OmerFaruk-Celik/ATILAY/atilay_kodlar/image.png

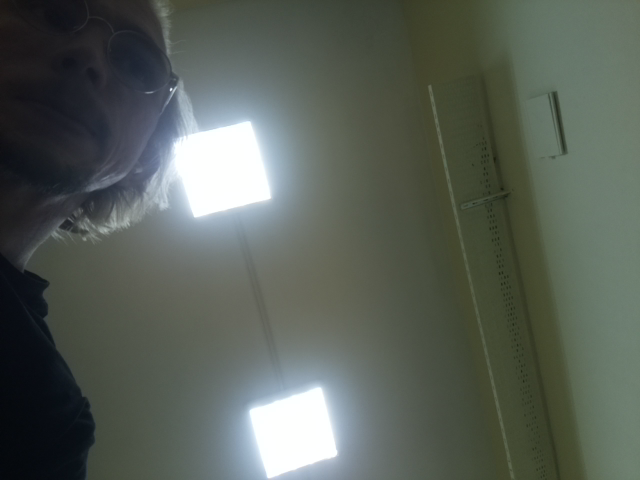
atilay_kodlar/image.png
