OmerFaruk-Celik/ATILAY/ProjeResimleri/IMG-20240529-WA0002.jpg

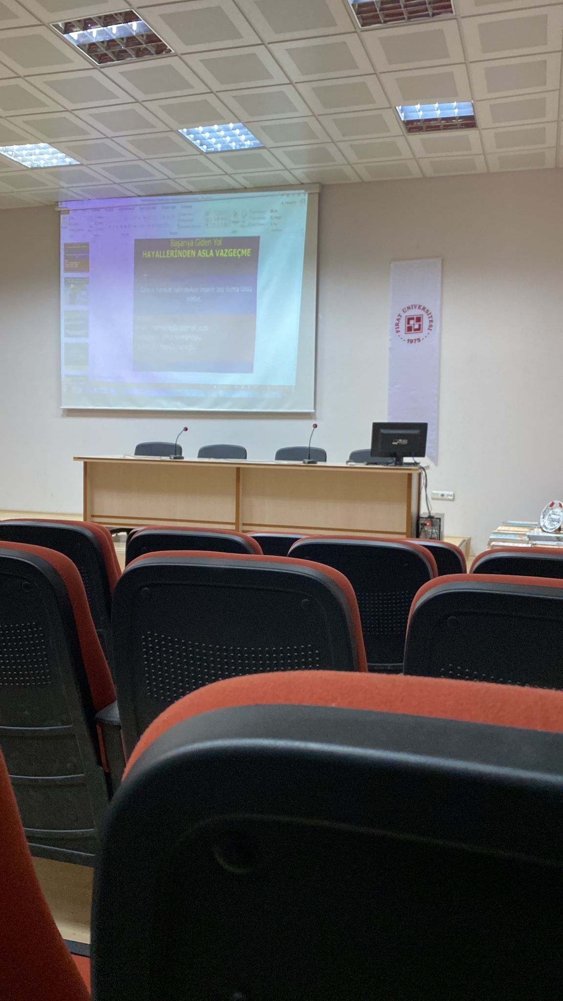
ProjeResimleri/IMG-20240529-WA0002.jpg
