OmerFaruk-Celik/ATILAY/ProjeResimleri/IMG-20240602-WA0001.jpg

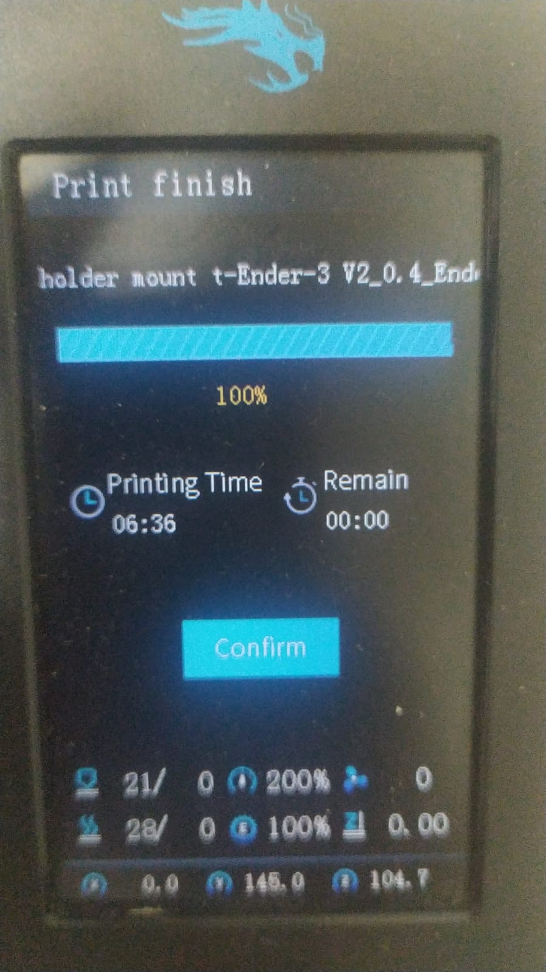
ProjeResimleri/IMG-20240602-WA0001.jpg
