OmerFaruk-Celik/ATILAY/ProjeResimleri/IMG-20240603-WA0001.jpg

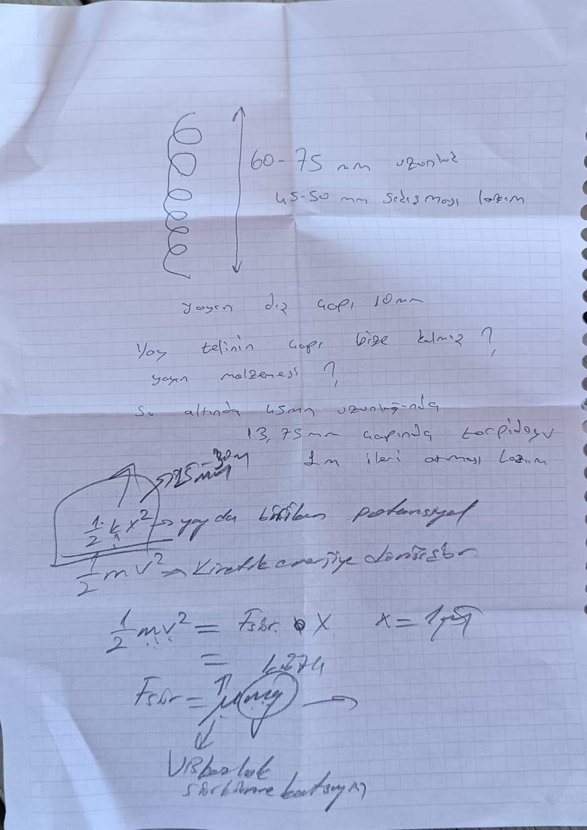
ProjeResimleri/IMG-20240603-WA0001.jpg
