OmerFaruk-Celik/ATILAY/ProjeResimleri/IMG-20240604-WA0000.jpg

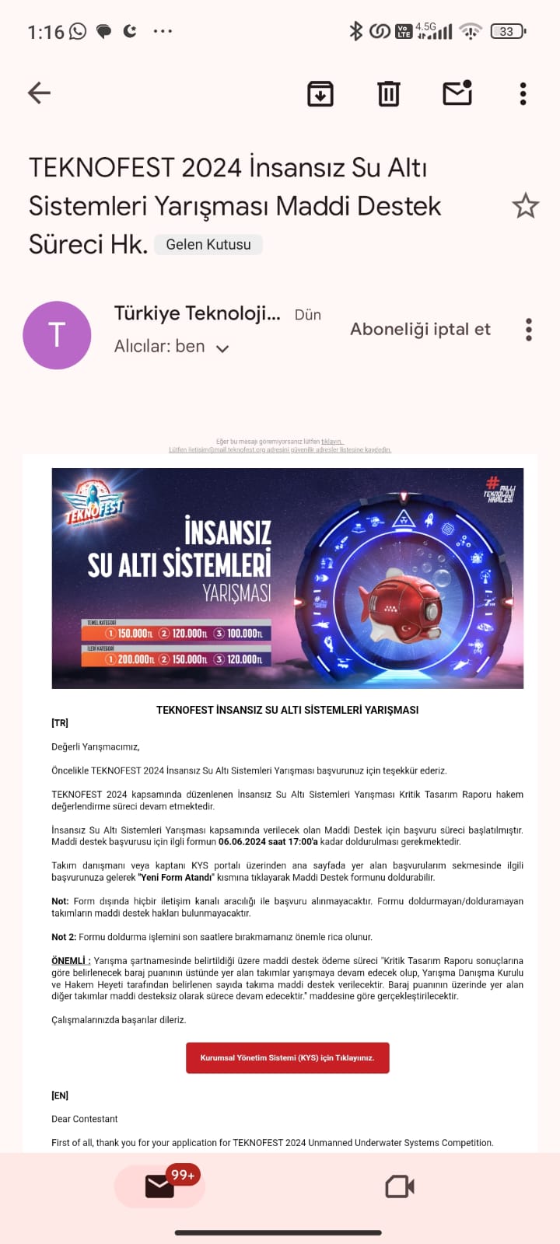
ProjeResimleri/IMG-20240604-WA0000.jpg
