OmerFaruk-Celik/ATILAY/ProjeResimleri/IMG-20240604-WA0001.jpg

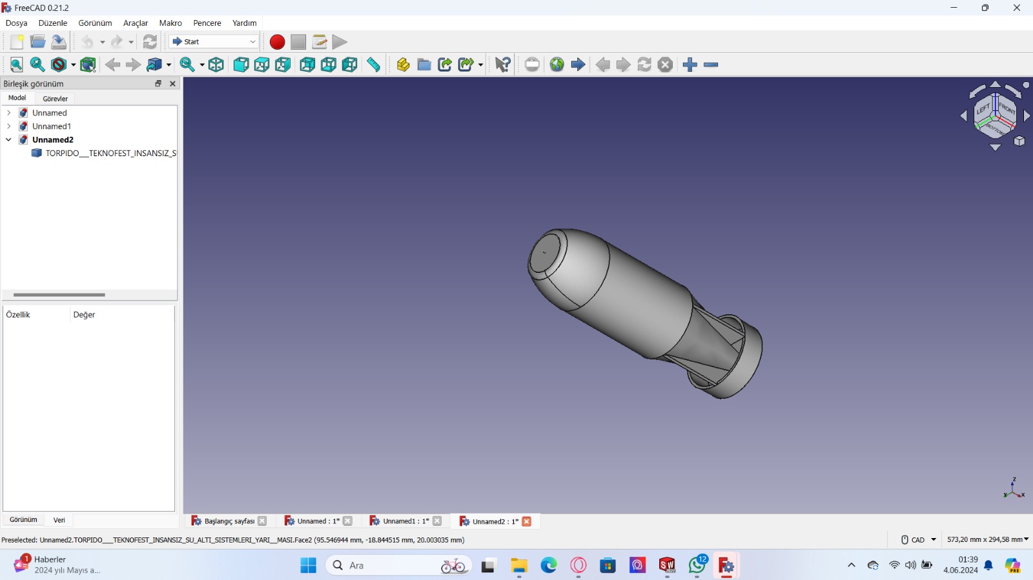
ProjeResimleri/IMG-20240604-WA0001.jpg
