OmerFaruk-Celik/ATILAY/ProjeResimleri/IMG-20240604-WA0003.jpg

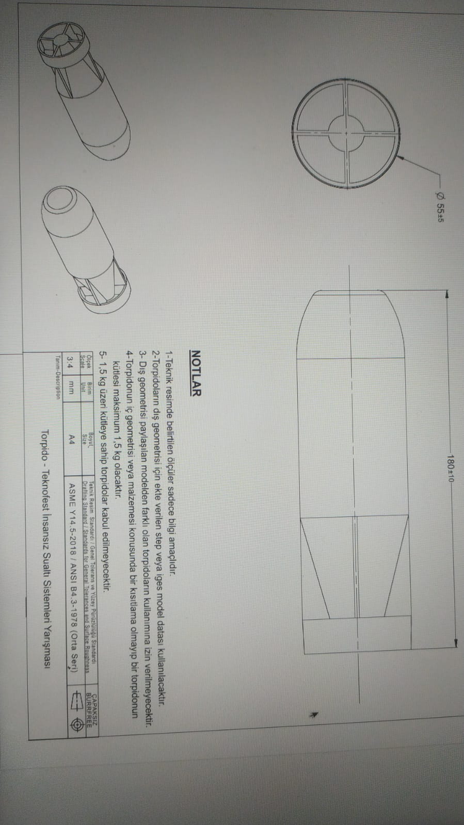
ProjeResimleri/IMG-20240604-WA0003.jpg
