OmerFaruk-Celik/ATILAY/ProjeResimleri/IMG-20240604-WA0005.jpg

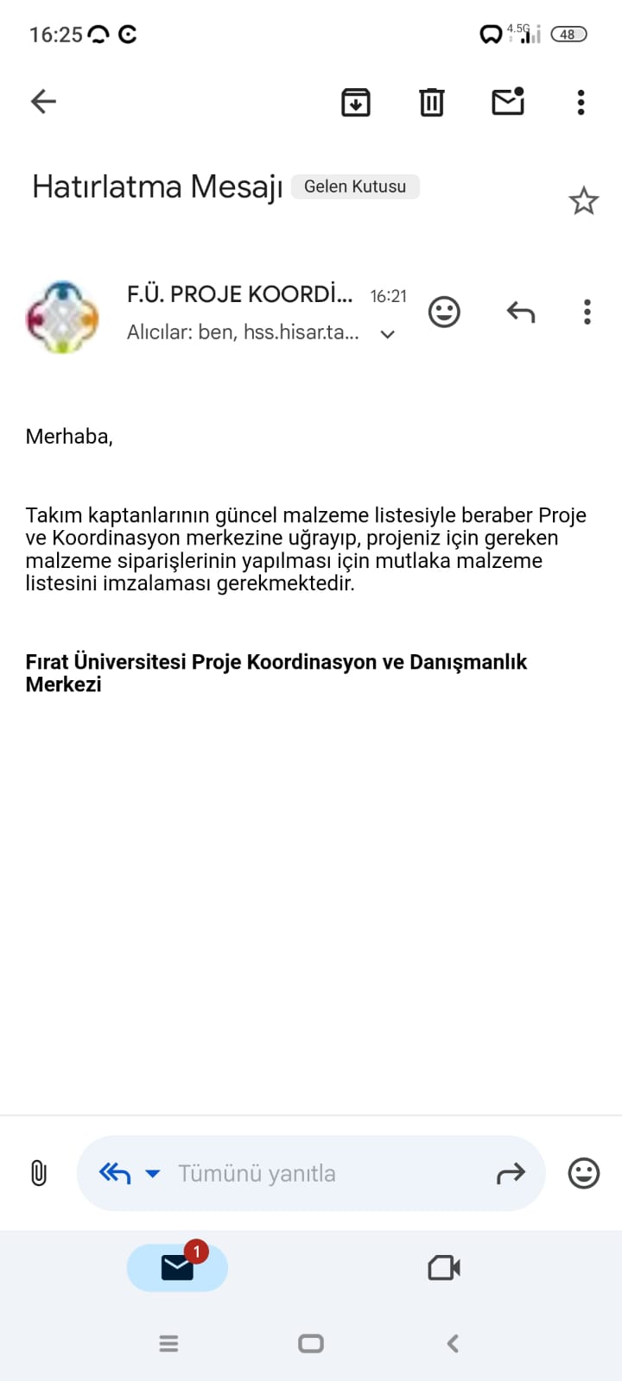
ProjeResimleri/IMG-20240604-WA0005.jpg
