OmerFaruk-Celik/ATILAY/ProjeResimleri/IMG-20240604-WA0007.jpg

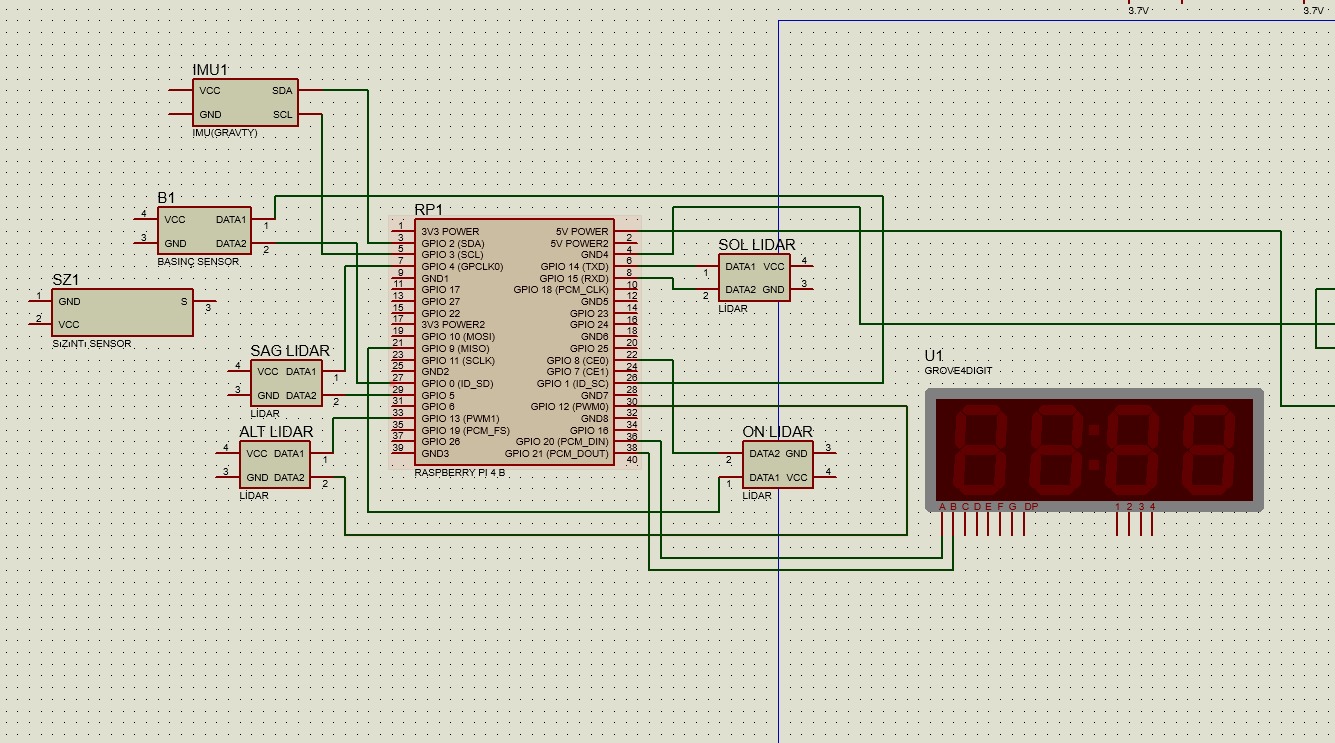
ProjeResimleri/IMG-20240604-WA0007.jpg
