OmerFaruk-Celik/ATILAY/ProjeResimleri/IMG-20240604-WA0008.jpg

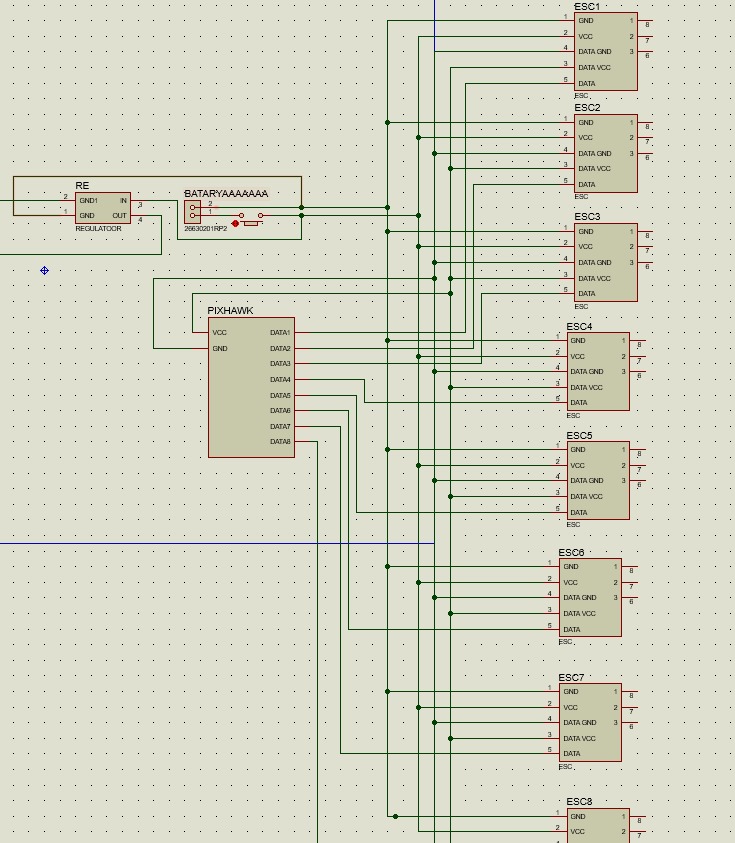
ProjeResimleri/IMG-20240604-WA0008.jpg
