OmerFaruk-Celik/ATILAY/ProjeResimleri/IMG-20240604-WA0009.jpg

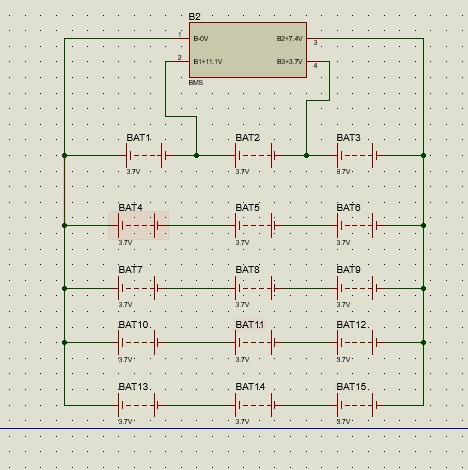
ProjeResimleri/IMG-20240604-WA0009.jpg
