OmerFaruk-Celik/ATILAY/ProjeResimleri/IMG-20240604-WA0010.jpg

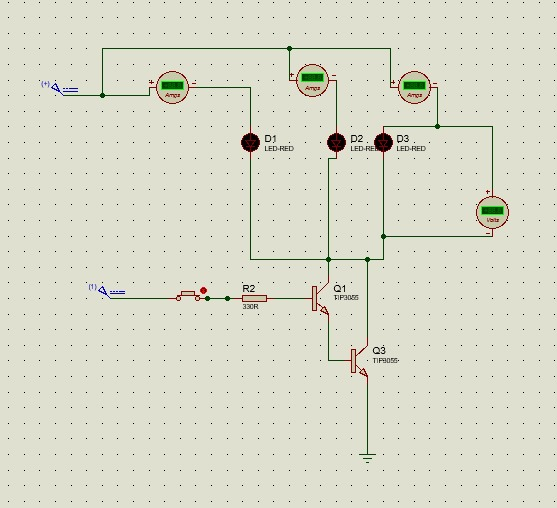
ProjeResimleri/IMG-20240604-WA0010.jpg
