OmerFaruk-Celik/ATILAY/ProjeResimleri/IMG-20240604-WA0011.jpg

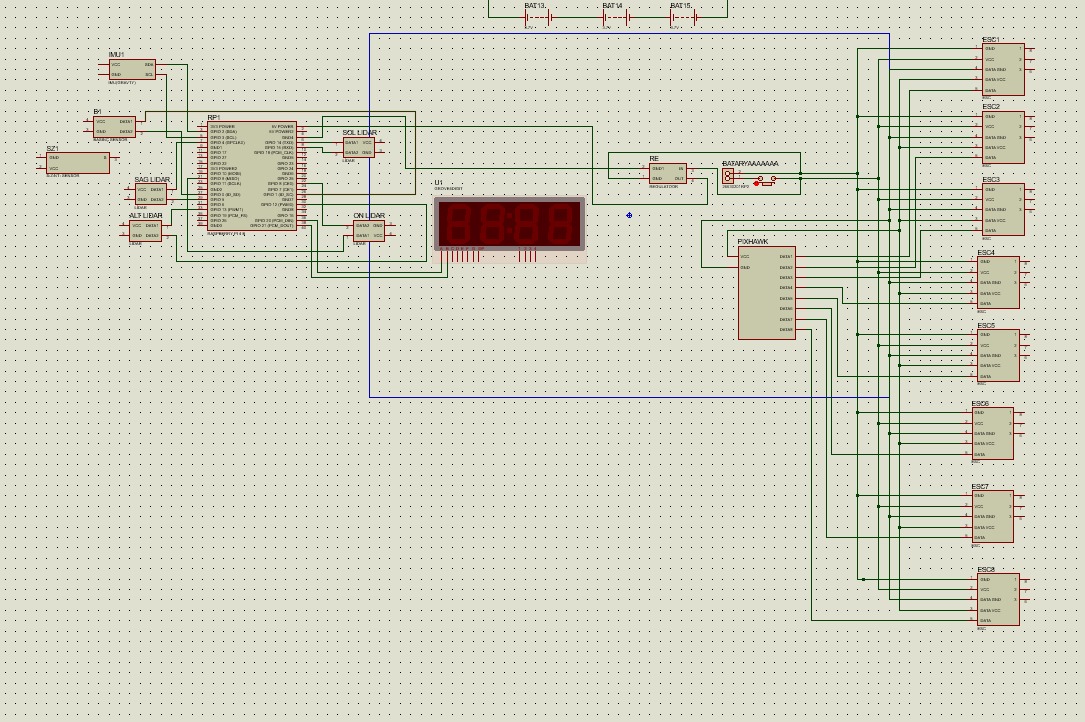
ProjeResimleri/IMG-20240604-WA0011.jpg
