OmerFaruk-Celik/ATILAY/ProjeResimleri/IMG-20240604-WA0039.jpg

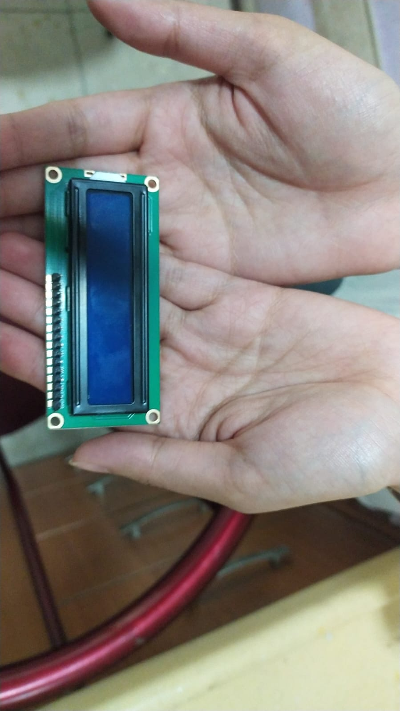
ProjeResimleri/IMG-20240604-WA0039.jpg
