OmerFaruk-Celik/ATILAY/ProjeResimleri/IMG-20240604-WA0040.jpg

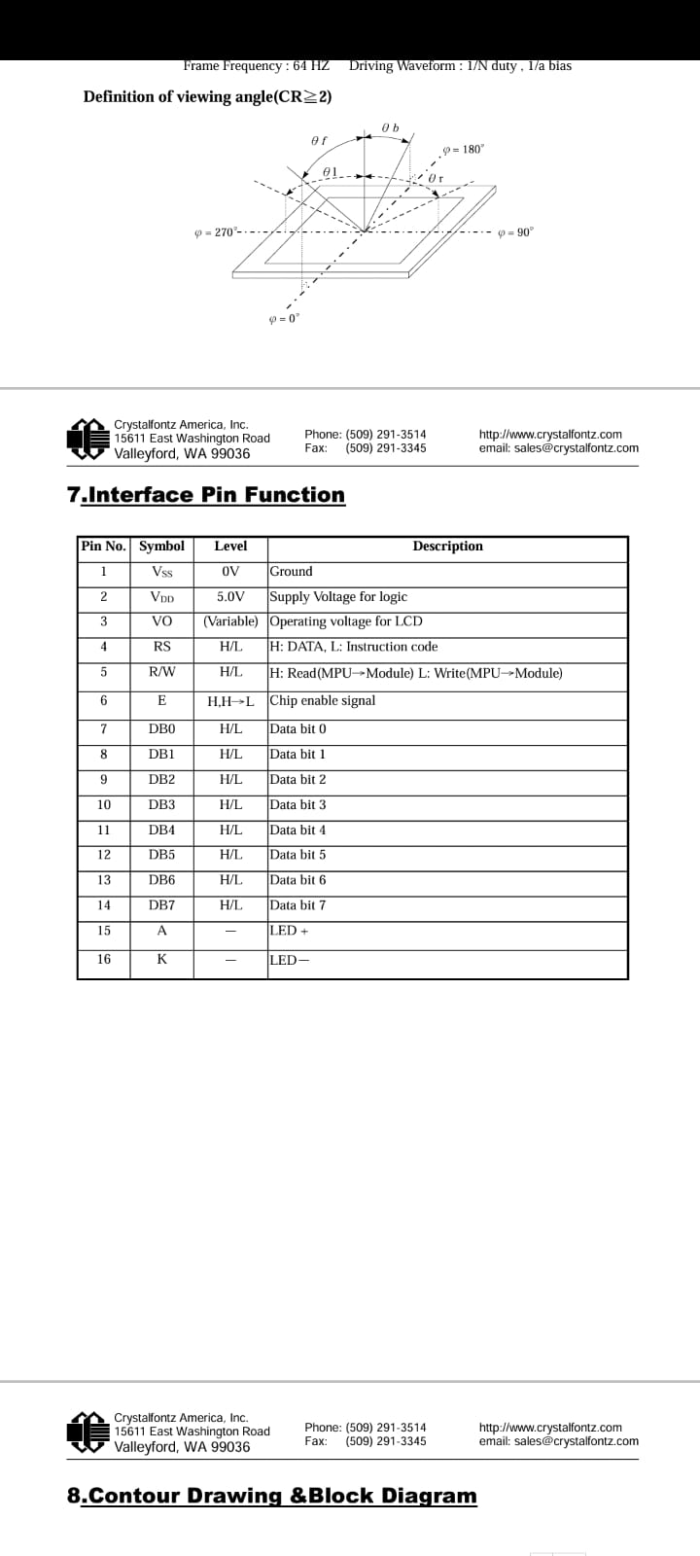
ProjeResimleri/IMG-20240604-WA0040.jpg
