OmerFaruk-Celik/ATILAY/ProjeResimleri/IMG-20240606-WA0000.jpg

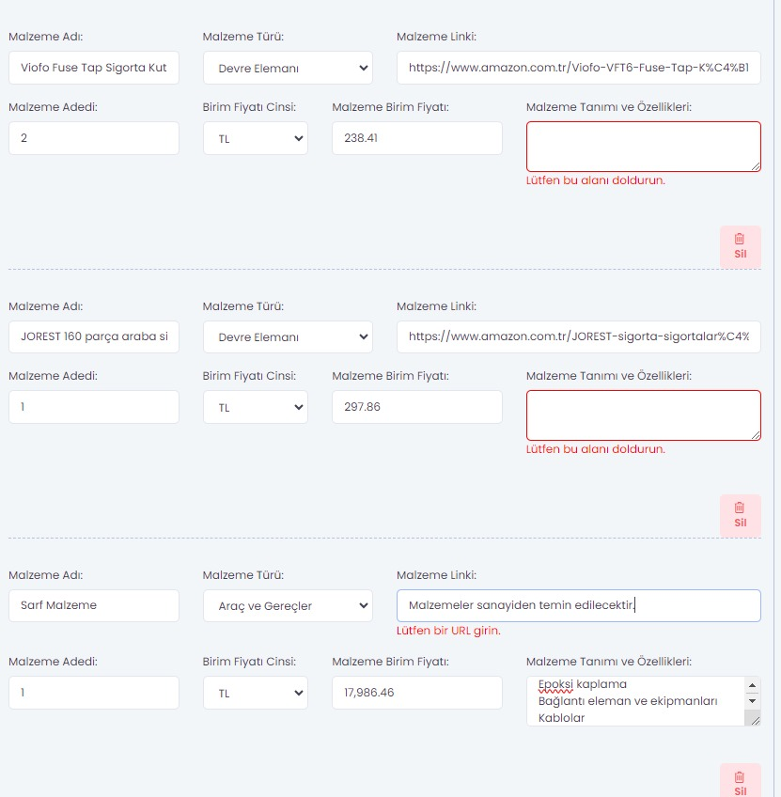
ProjeResimleri/IMG-20240606-WA0000.jpg
