OmerFaruk-Celik/ATILAY/ProjeResimleri/IMG-20240606-WA0001.jpg

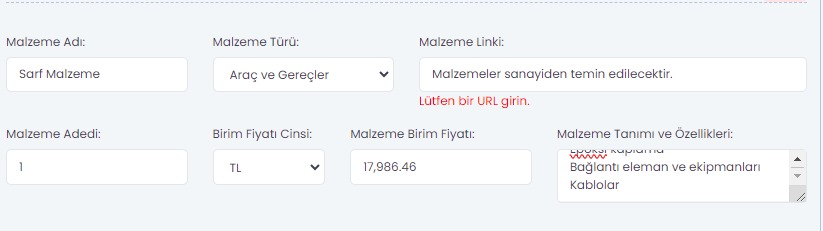
ProjeResimleri/IMG-20240606-WA0001.jpg
