OmerFaruk-Celik/ATILAY/ProjeResimleri/IMG-20240608-WA0016.jpg

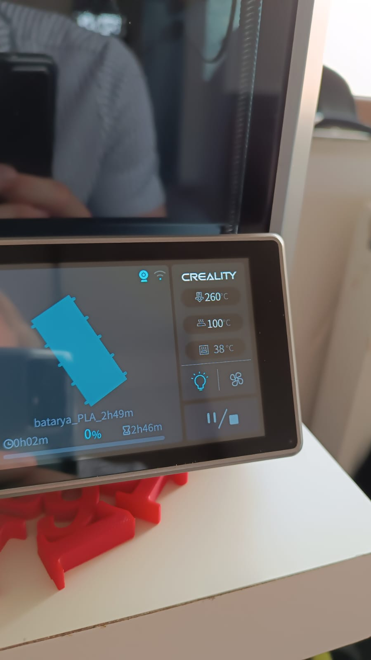
ProjeResimleri/IMG-20240608-WA0016.jpg
