OmerFaruk-Celik/ATILAY/ProjeResimleri/IMG-20240608-WA0018.jpg

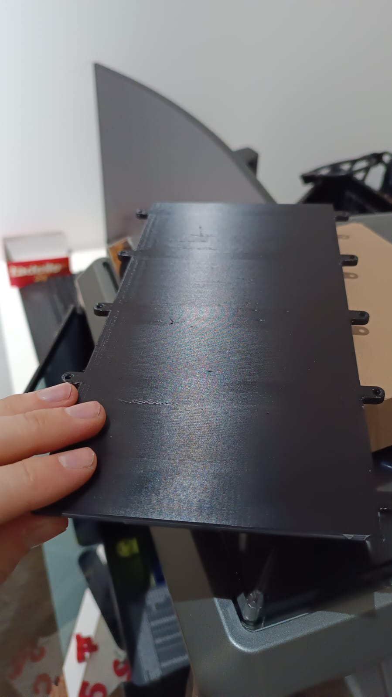
ProjeResimleri/IMG-20240608-WA0018.jpg
