OmerFaruk-Celik/ATILAY/ProjeResimleri/IMG-20240608-WA0019.jpg

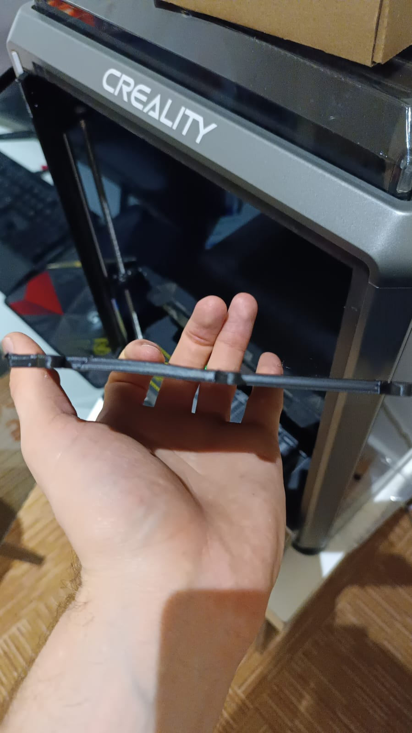
ProjeResimleri/IMG-20240608-WA0019.jpg
