OmerFaruk-Celik/ATILAY/ProjeResimleri/IMG-20240609-WA0012.jpg

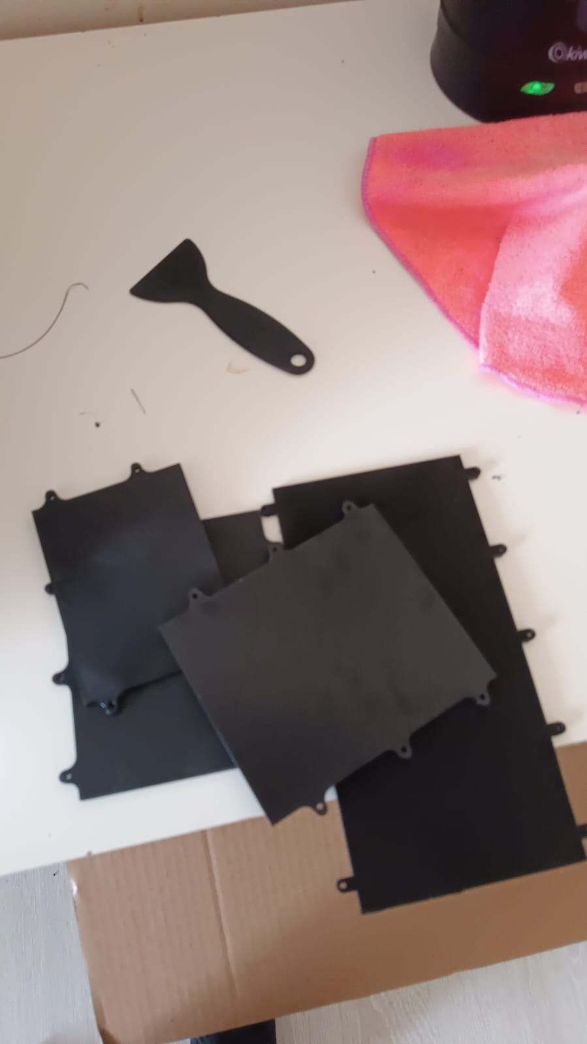
ProjeResimleri/IMG-20240609-WA0012.jpg
