OmerFaruk-Celik/ATILAY/ProjeResimleri/IMG-20240609-WA0013.jpg

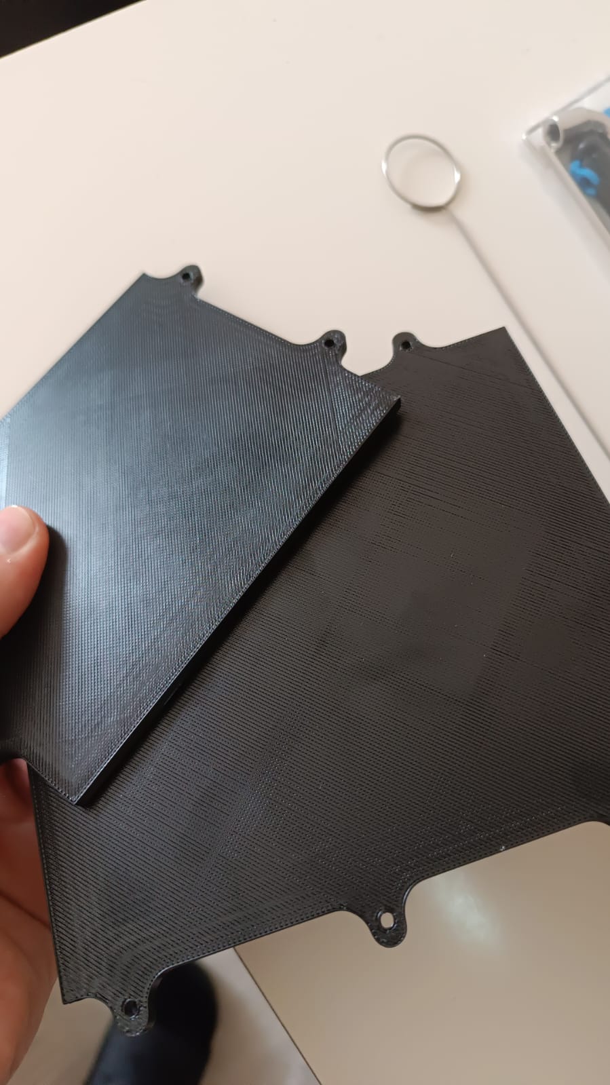
ProjeResimleri/IMG-20240609-WA0013.jpg
