OmerFaruk-Celik/ATILAY/ProjeResimleri/IMG-20240609-WA0015.jpg

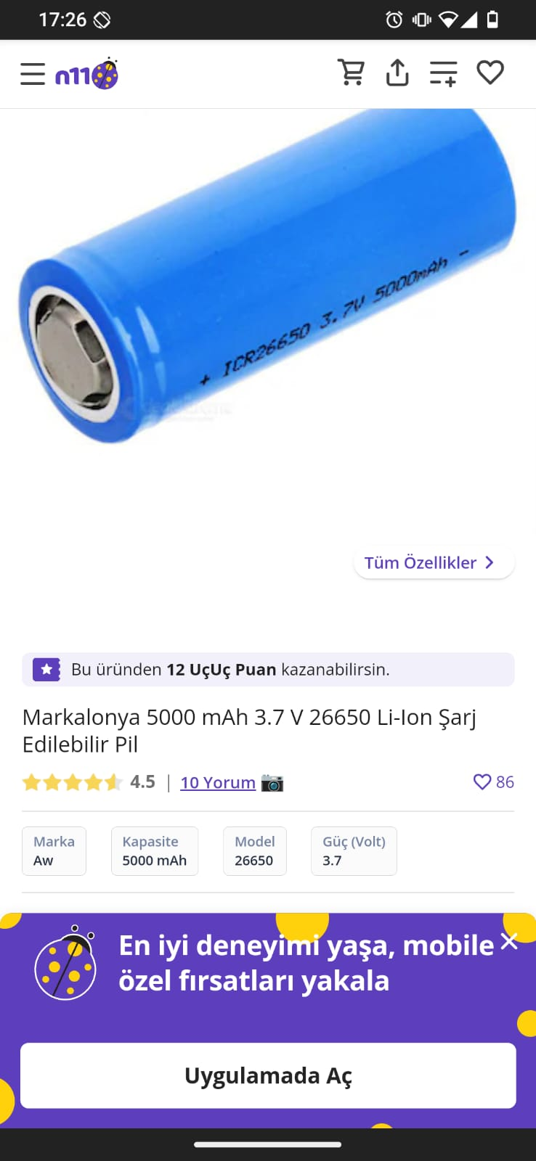
ProjeResimleri/IMG-20240609-WA0015.jpg
