OmerFaruk-Celik/ATILAY/ProjeResimleri/IMG-20240609-WA0017.jpg

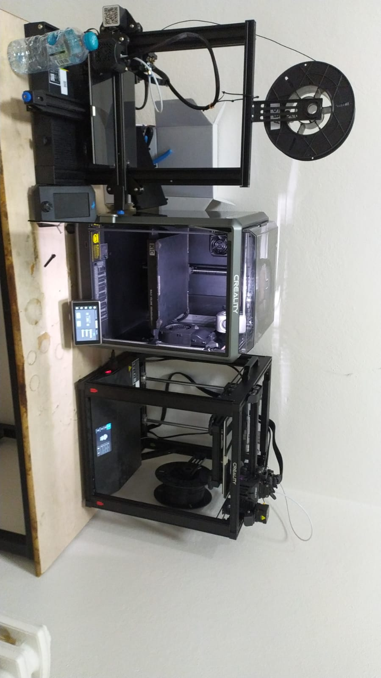
ProjeResimleri/IMG-20240609-WA0017.jpg
