OmerFaruk-Celik/ATILAY/ProjeResimleri/IMG-20240610-WA0000.jpg

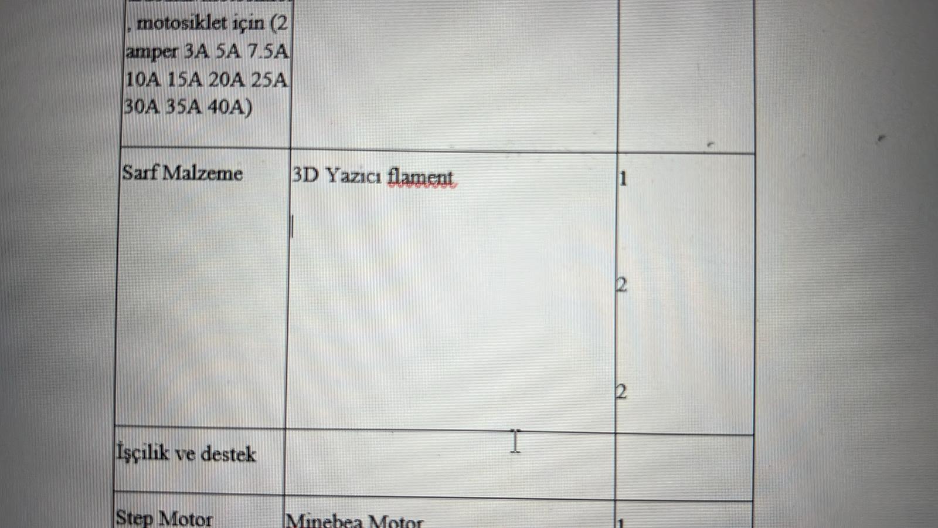
ProjeResimleri/IMG-20240610-WA0000.jpg
