OmerFaruk-Celik/ATILAY/ProjeResimleri/IMG-20240610-WA0002.jpg

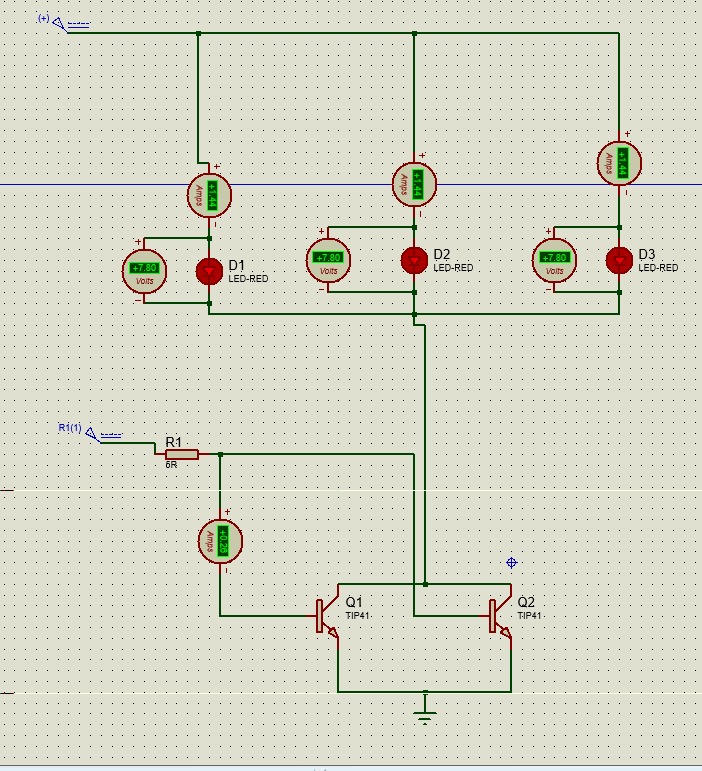
ProjeResimleri/IMG-20240610-WA0002.jpg
