OmerFaruk-Celik/ATILAY/ProjeResimleri/IMG-20240610-WA0004.jpg

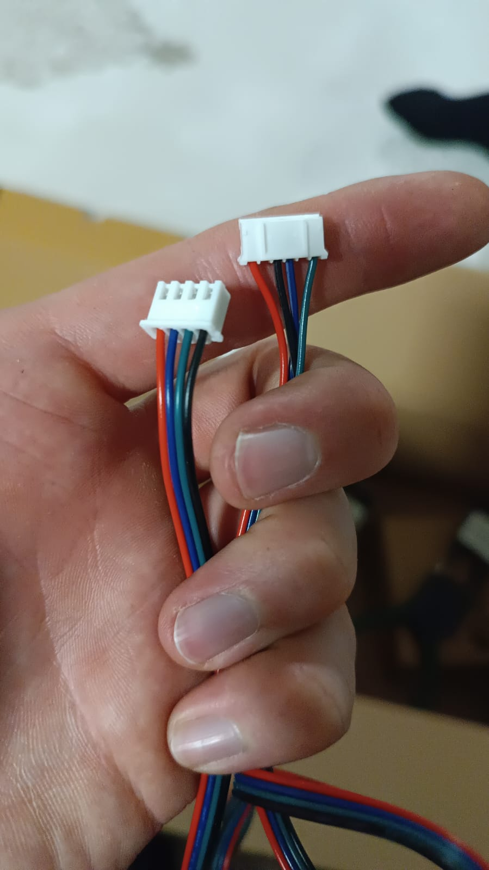
ProjeResimleri/IMG-20240610-WA0004.jpg
