OmerFaruk-Celik/ATILAY/ProjeResimleri/IMG-20240610-WA0005.jpg

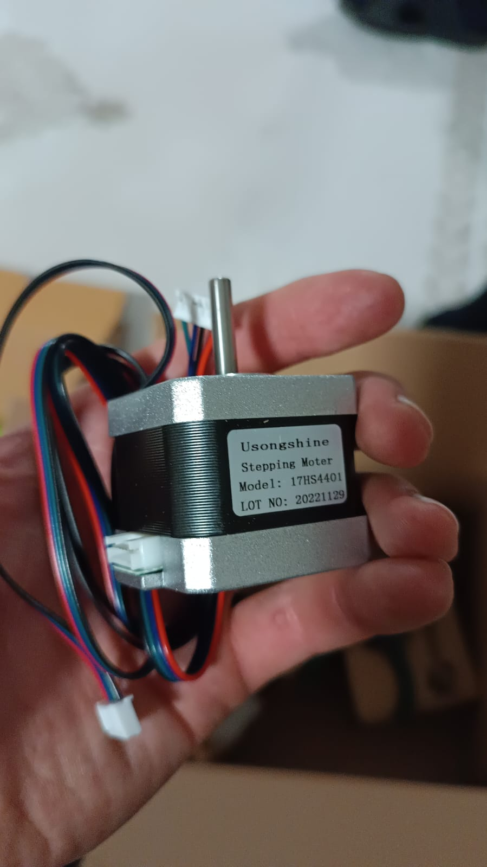
ProjeResimleri/IMG-20240610-WA0005.jpg
