OmerFaruk-Celik/ATILAY/ProjeResimleri/IMG-20240611-WA0004.jpg

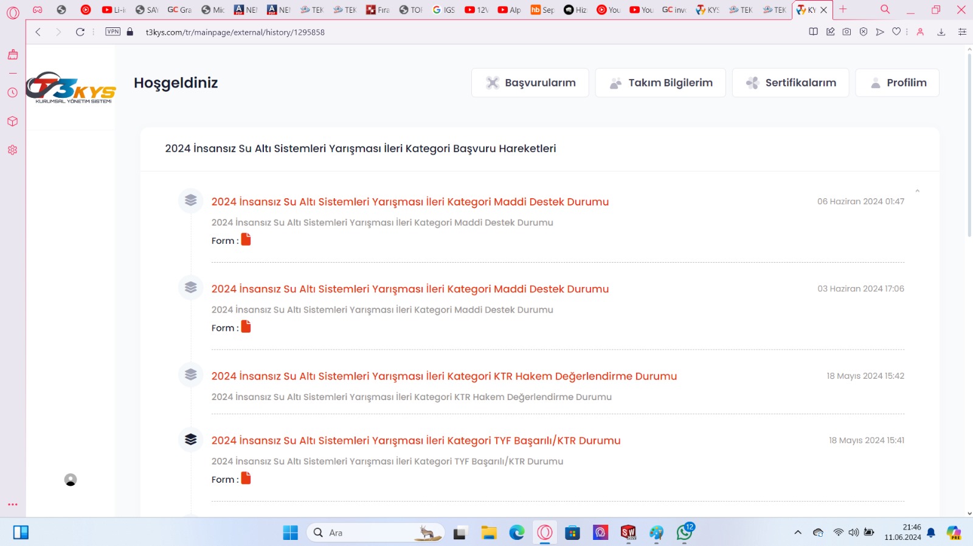
ProjeResimleri/IMG-20240611-WA0004.jpg
