OmerFaruk-Celik/ATILAY/ProjeResimleri/IMG-20240611-WA0006.jpg

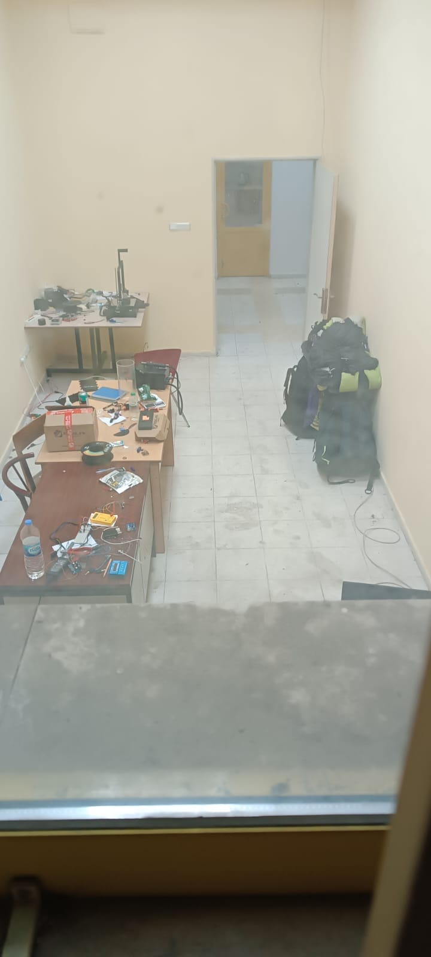
ProjeResimleri/IMG-20240611-WA0006.jpg
