OmerFaruk-Celik/ATILAY/ProjeResimleri/IMG-20240612-WA0005.jpg

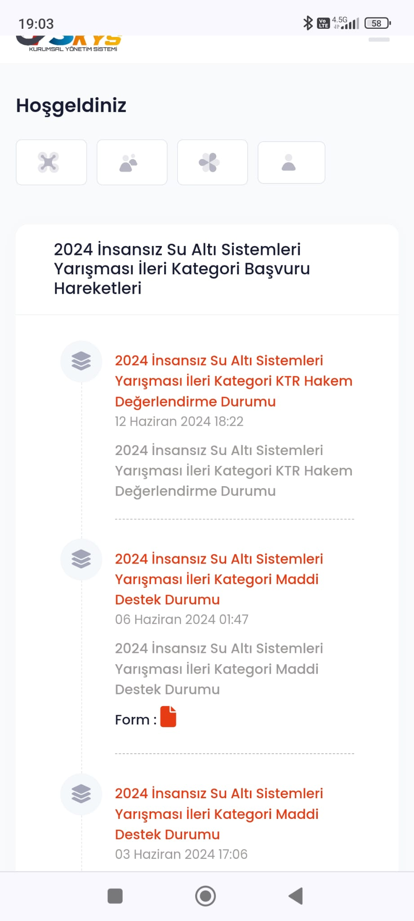
ProjeResimleri/IMG-20240612-WA0005.jpg
