OmerFaruk-Celik/ATILAY/ProjeResimleri/IMG-20240613-WA0009.jpg

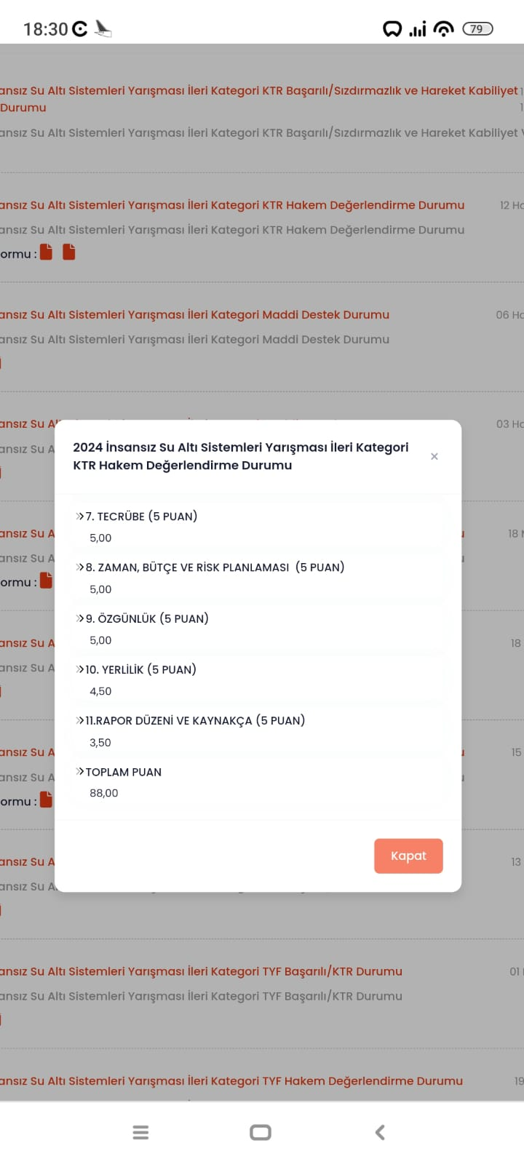
ProjeResimleri/IMG-20240613-WA0009.jpg
