OmerFaruk-Celik/ATILAY/ProjeResimleri/IMG-20240613-WA0010.jpg

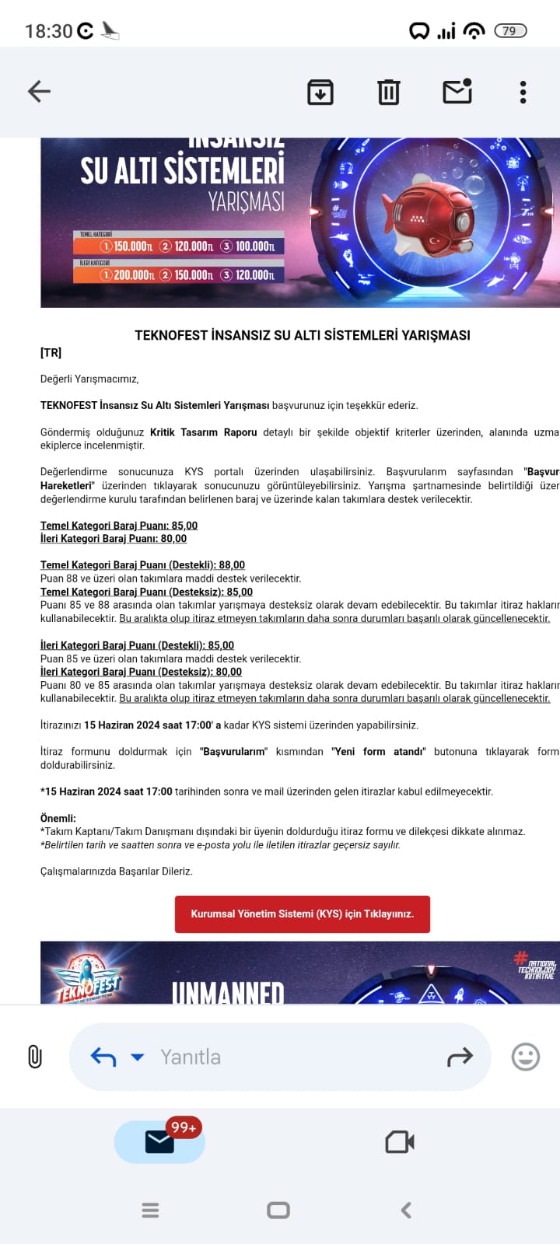
ProjeResimleri/IMG-20240613-WA0010.jpg
