OmerFaruk-Celik/ATILAY/ProjeResimleri/IMG-20240613-WA0028.jpg

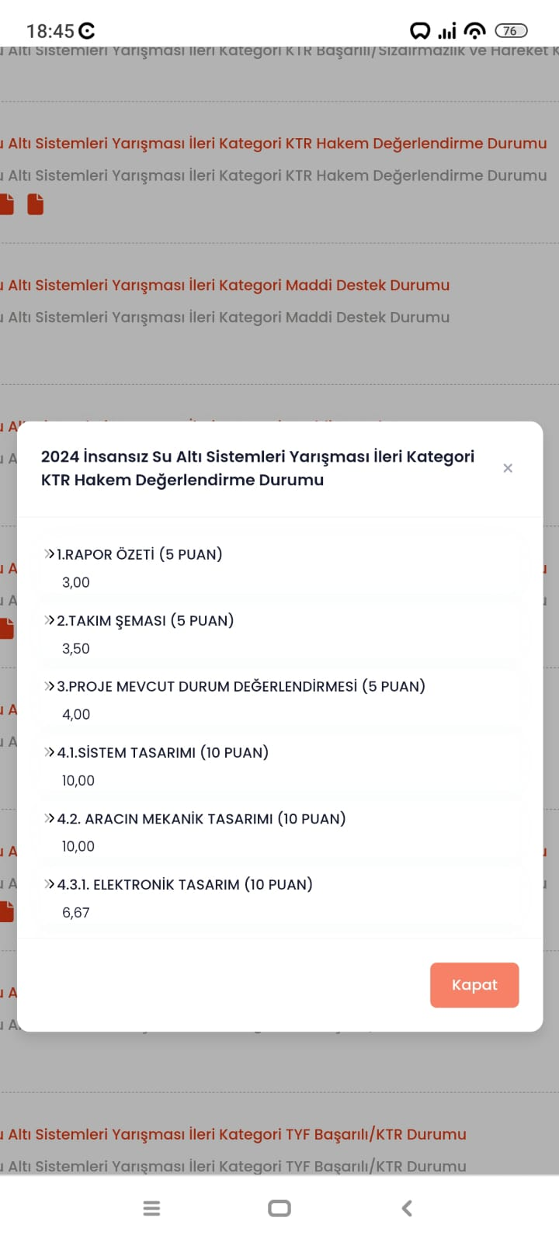
ProjeResimleri/IMG-20240613-WA0028.jpg
