OmerFaruk-Celik/ATILAY/ProjeResimleri/IMG-20240613-WA0029.jpg

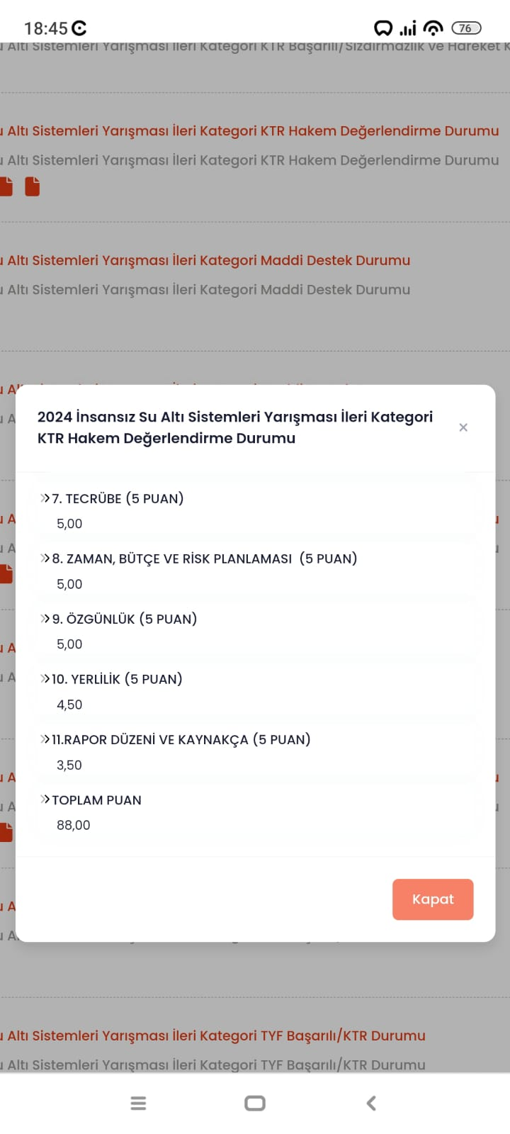
ProjeResimleri/IMG-20240613-WA0029.jpg
