OmerFaruk-Celik/ATILAY/ProjeResimleri/IMG-20240613-WA0030.jpg

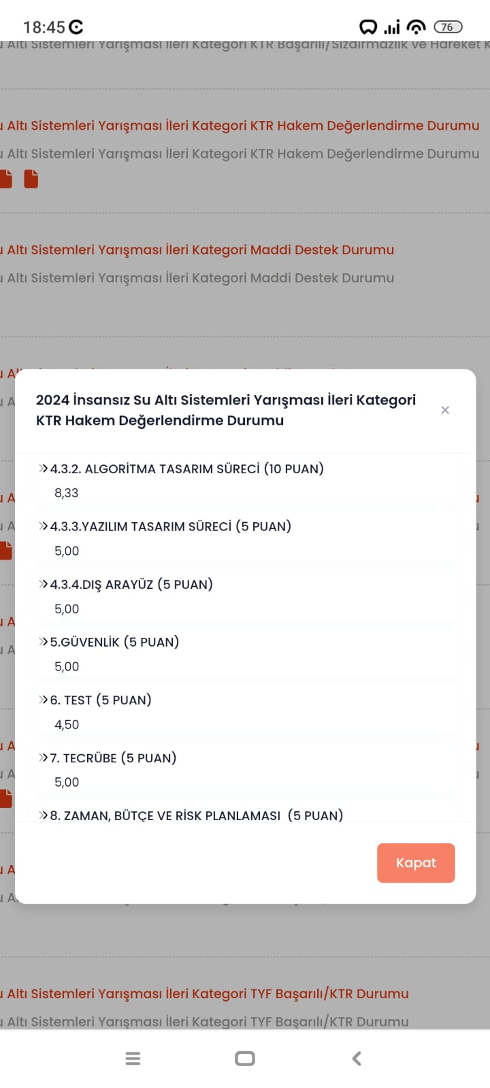
ProjeResimleri/IMG-20240613-WA0030.jpg
