OmerFaruk-Celik/ATILAY/ProjeResimleri/IMG-20240614-WA0005.jpg

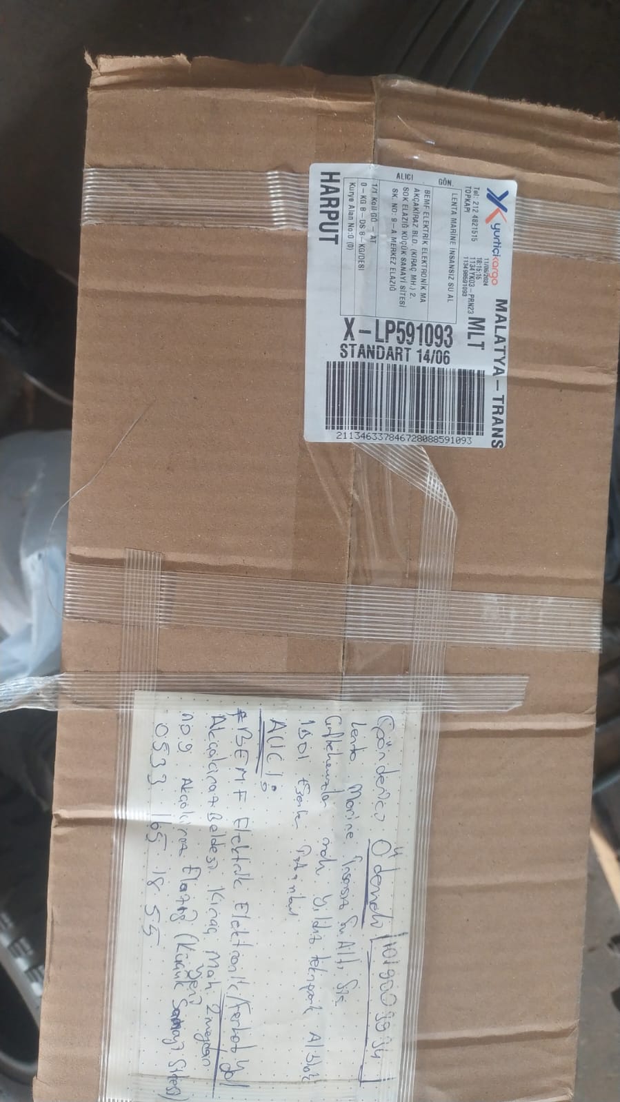
ProjeResimleri/IMG-20240614-WA0005.jpg
