OmerFaruk-Celik/ATILAY/ProjeResimleri/IMG-20240627-WA0004.jpg

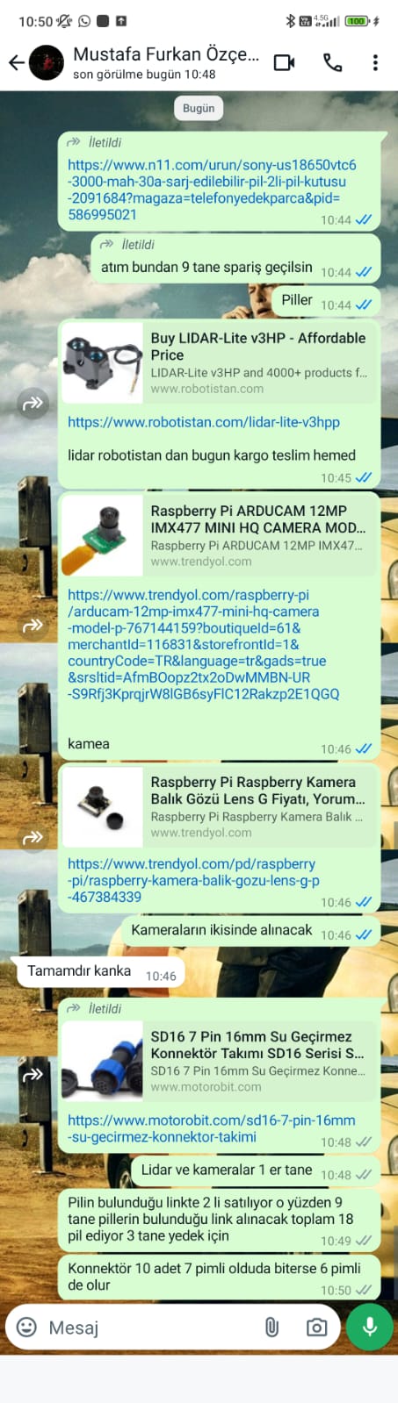
ProjeResimleri/IMG-20240627-WA0004.jpg
