OmerFaruk-Celik/ATILAY/ProjeResimleri/IMG-20240627-WA0005.jpg

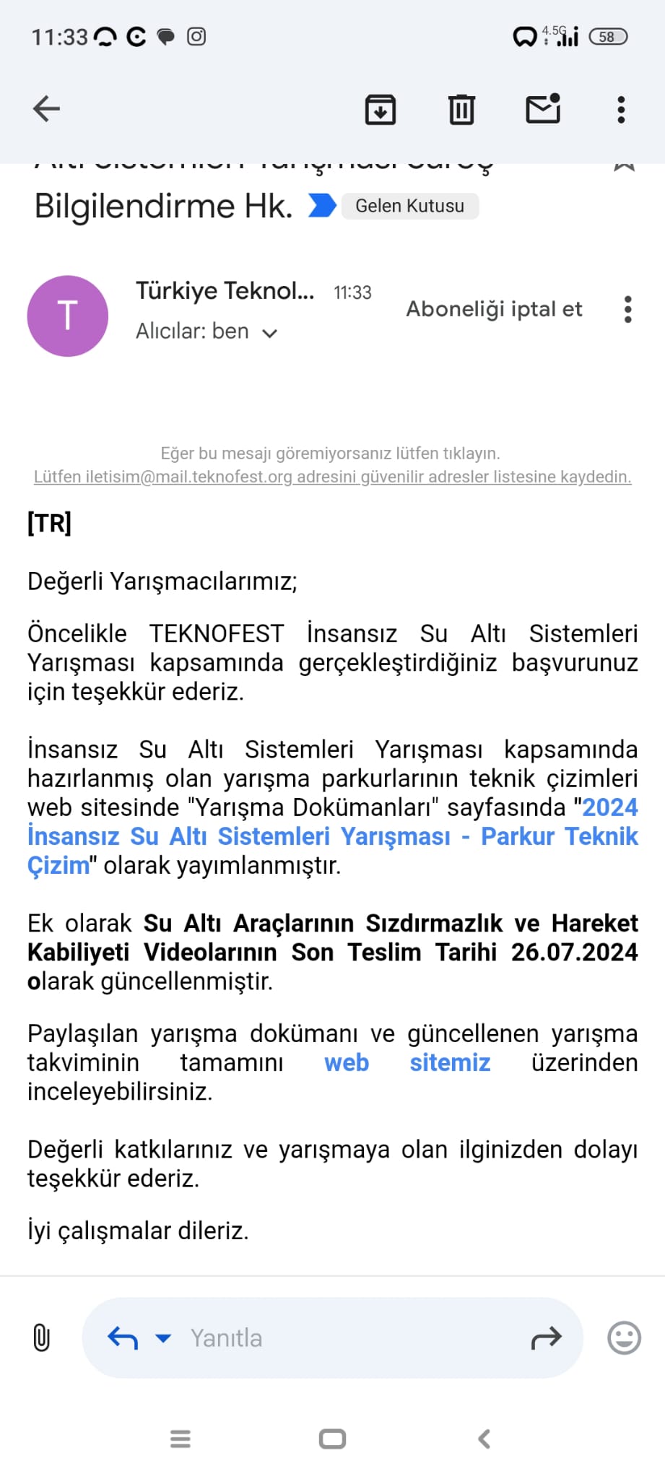
ProjeResimleri/IMG-20240627-WA0005.jpg
