OmerFaruk-Celik/ATILAY/ProjeResimleri/IMG-20240630-WA0005.jpg

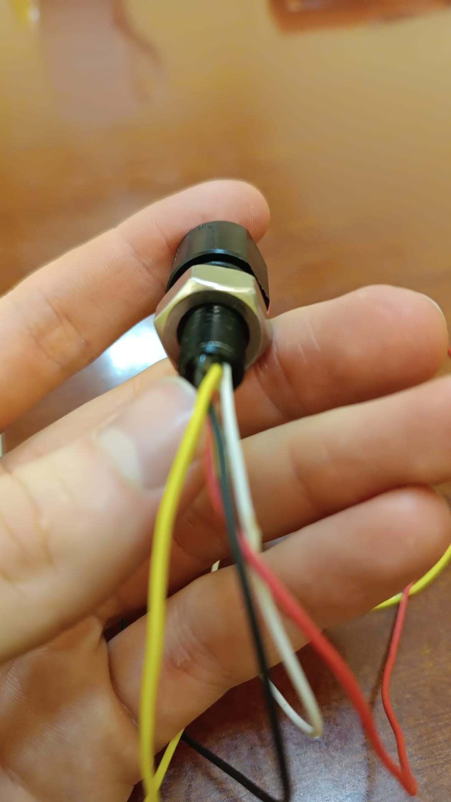
ProjeResimleri/IMG-20240630-WA0005.jpg
