OmerFaruk-Celik/ATILAY/ProjeResimleri/IMG-20240630-WA0006.jpg

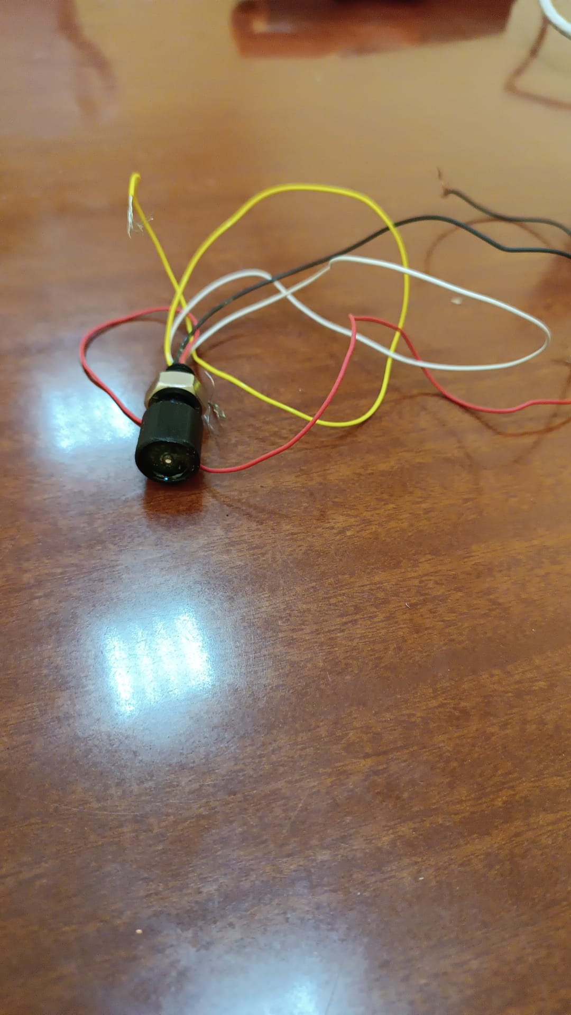
ProjeResimleri/IMG-20240630-WA0006.jpg
