OmerFaruk-Celik/ATILAY/ProjeResimleri/IMG-20240630-WA0007.jpg

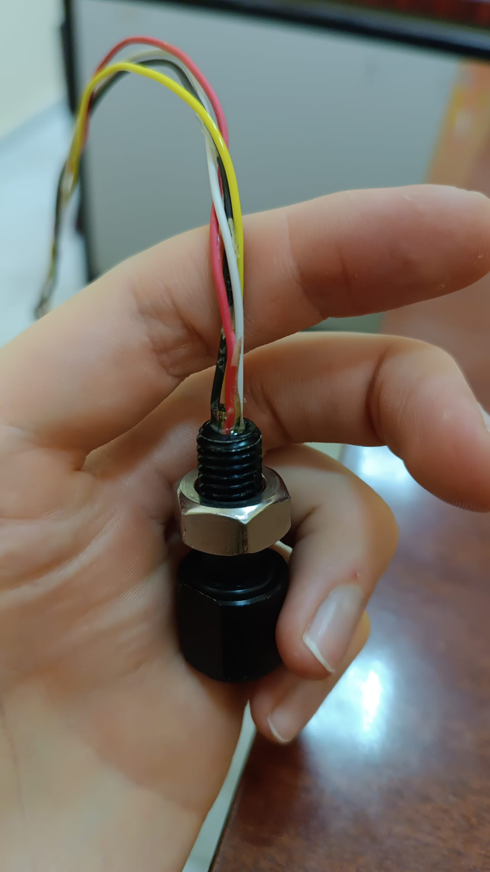
ProjeResimleri/IMG-20240630-WA0007.jpg
