OmerFaruk-Celik/ATILAY/ProjeResimleri/IMG-20240709-WA0001.jpg

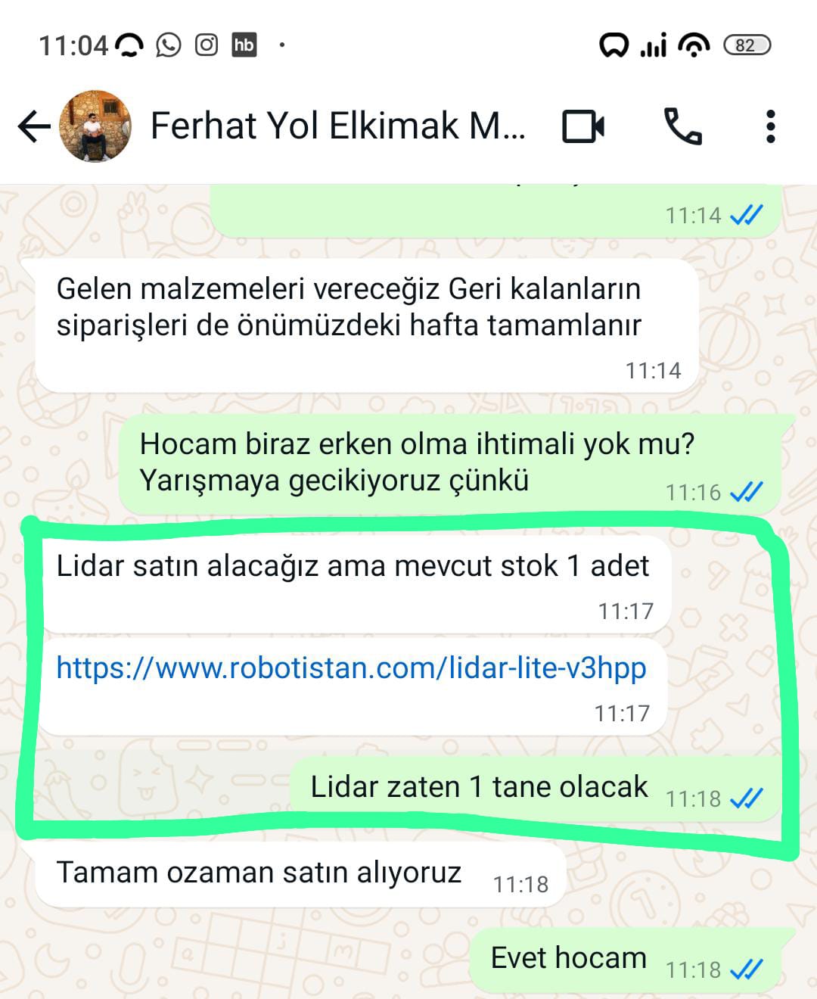
ProjeResimleri/IMG-20240709-WA0001.jpg
