OmerFaruk-Celik/ATILAY/ProjeResimleri/IMG-20240709-WA0003.jpg

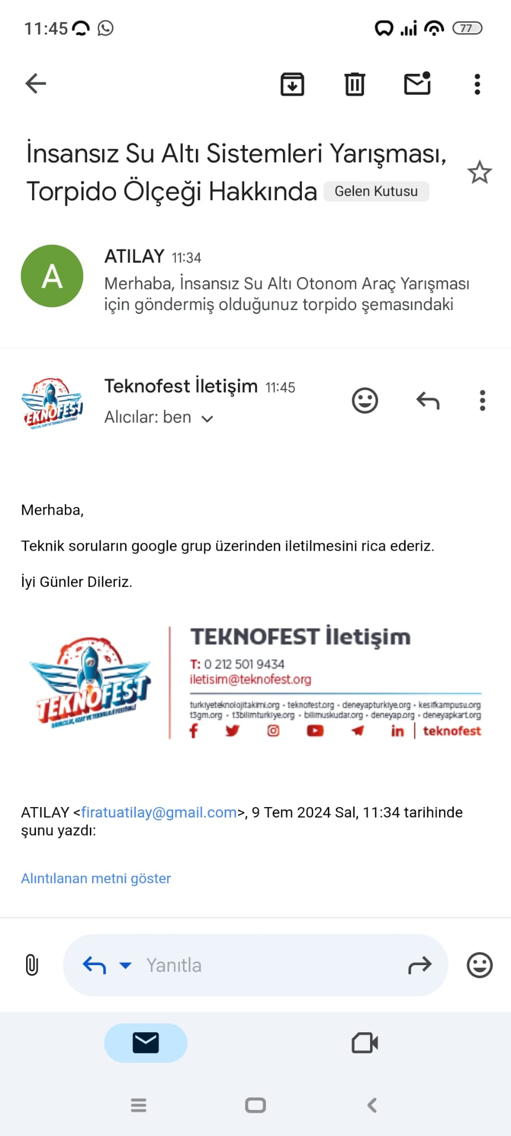
ProjeResimleri/IMG-20240709-WA0003.jpg
