OmerFaruk-Celik/ATILAY/ProjeResimleri/IMG-20240716-WA0026.jpg

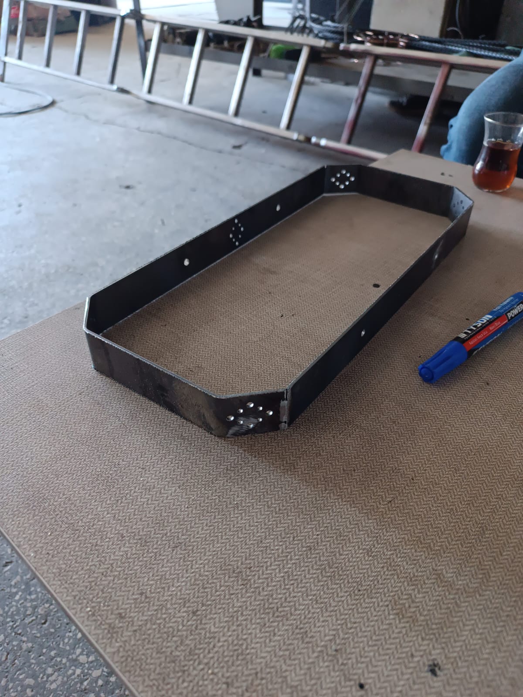
ProjeResimleri/IMG-20240716-WA0026.jpg
