OmerFaruk-Celik/ATILAY/ProjeResimleri/IMG-20240716-WA0027.jpg

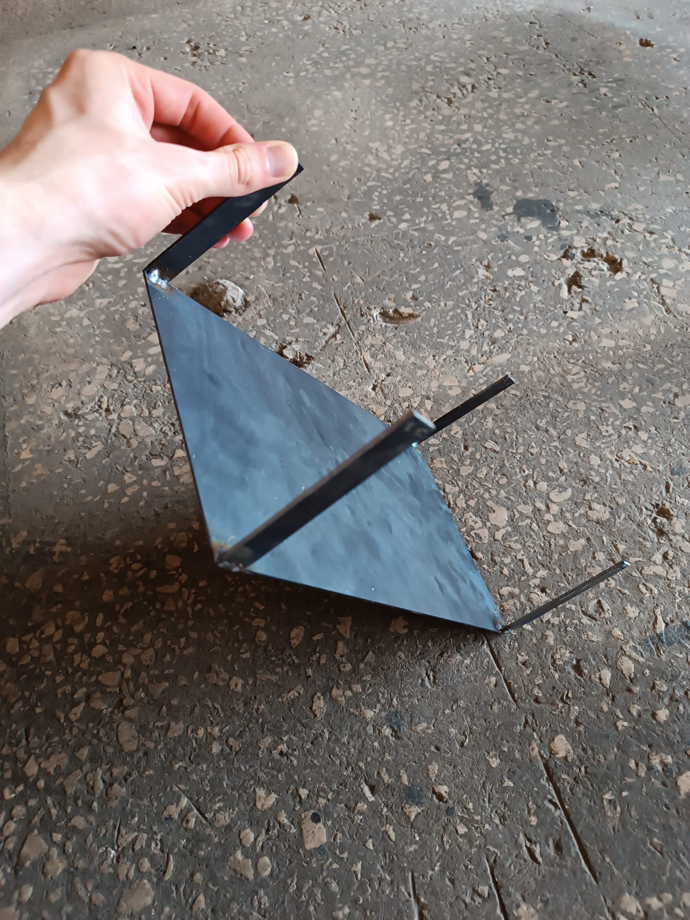
ProjeResimleri/IMG-20240716-WA0027.jpg
