OmerFaruk-Celik/ATILAY/ProjeResimleri/IMG-20240716-WA0031.jpg

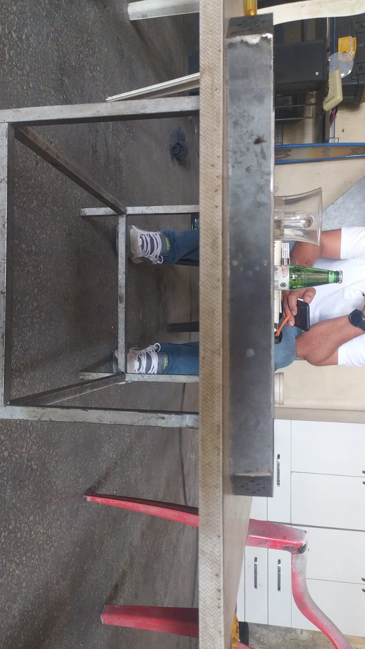
ProjeResimleri/IMG-20240716-WA0031.jpg
