OmerFaruk-Celik/ATILAY/ProjeResimleri/IMG-20240716-WA0033.jpg

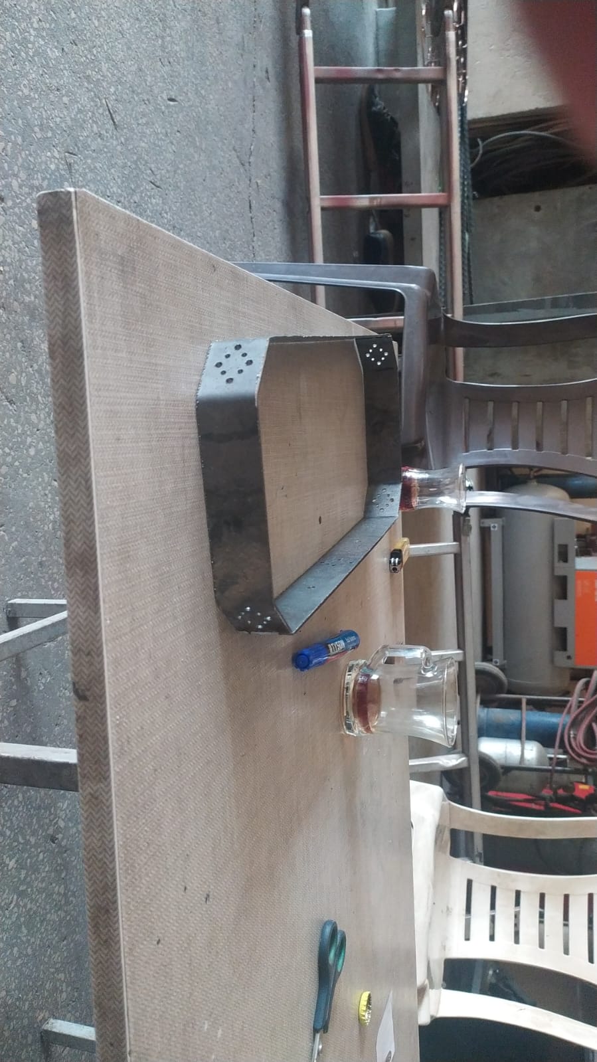
ProjeResimleri/IMG-20240716-WA0033.jpg
