OmerFaruk-Celik/ATILAY/ProjeResimleri/IMG-20240716-WA0035.jpg

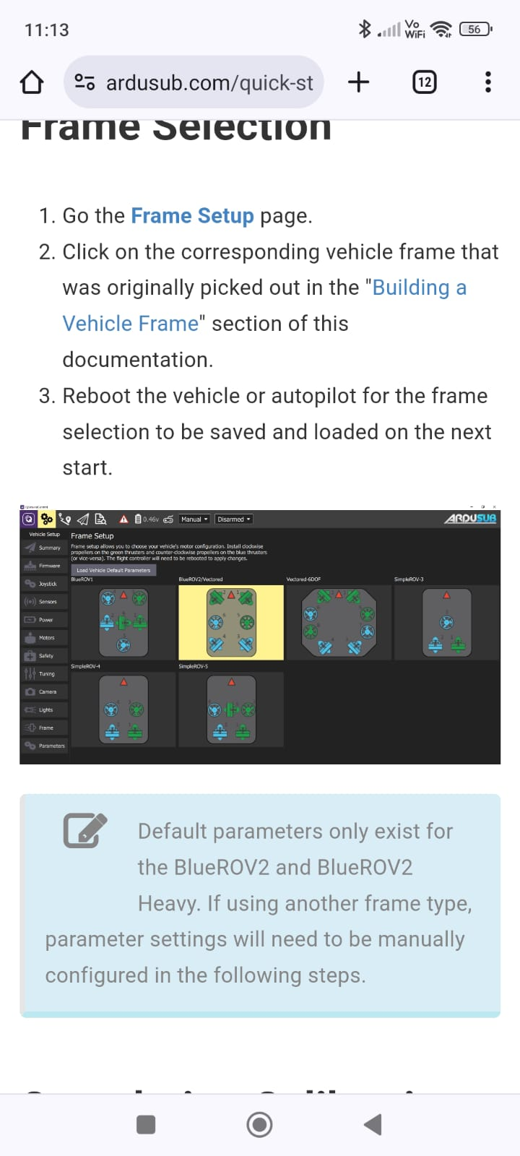
ProjeResimleri/IMG-20240716-WA0035.jpg
