OmerFaruk-Celik/ATILAY/ProjeResimleri/IMG-20240716-WA0044.jpg

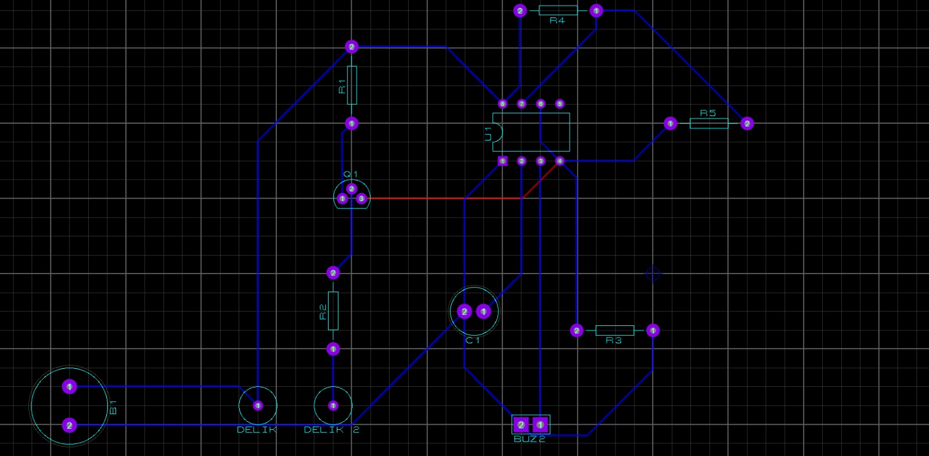
ProjeResimleri/IMG-20240716-WA0044.jpg
