OmerFaruk-Celik/ATILAY/ProjeResimleri/IMG-20240717-WA0003.jpg

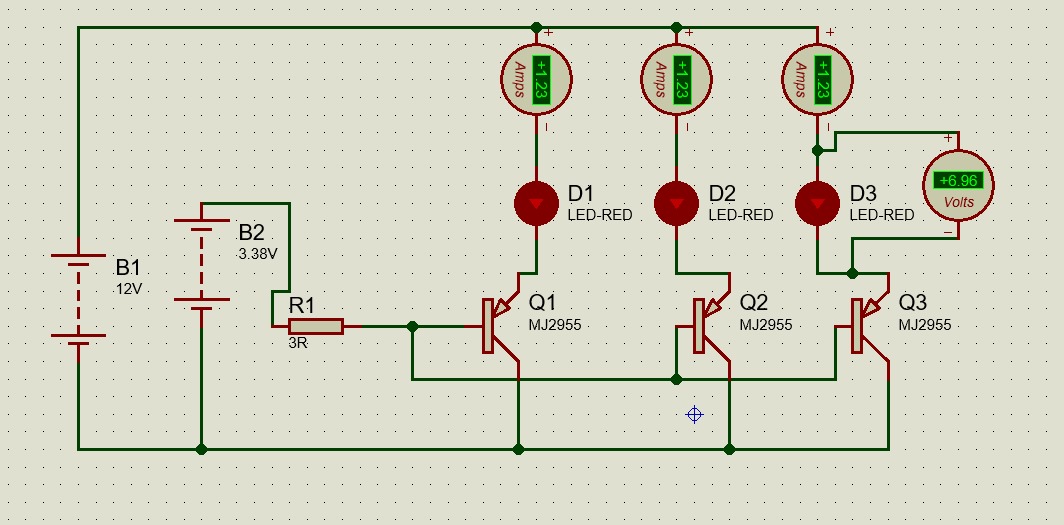
ProjeResimleri/IMG-20240717-WA0003.jpg
