OmerFaruk-Celik/ATILAY/ProjeResimleri/IMG-20240718-WA0010.jpg

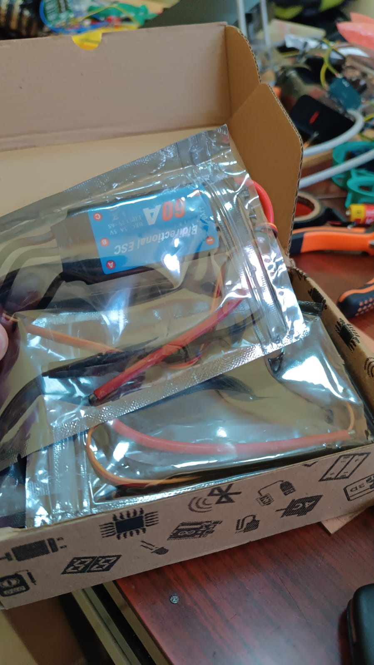
ProjeResimleri/IMG-20240718-WA0010.jpg
