OmerFaruk-Celik/ATILAY/ProjeResimleri/IMG-20240720-WA0003.jpg

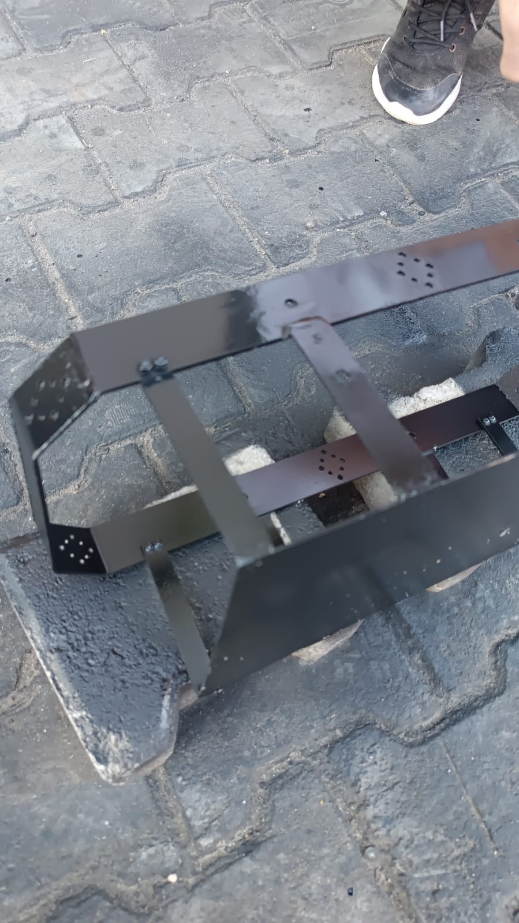
ProjeResimleri/IMG-20240720-WA0003.jpg
