OmerFaruk-Celik/ATILAY/ProjeResimleri/IMG-20240722-WA0004.jpg

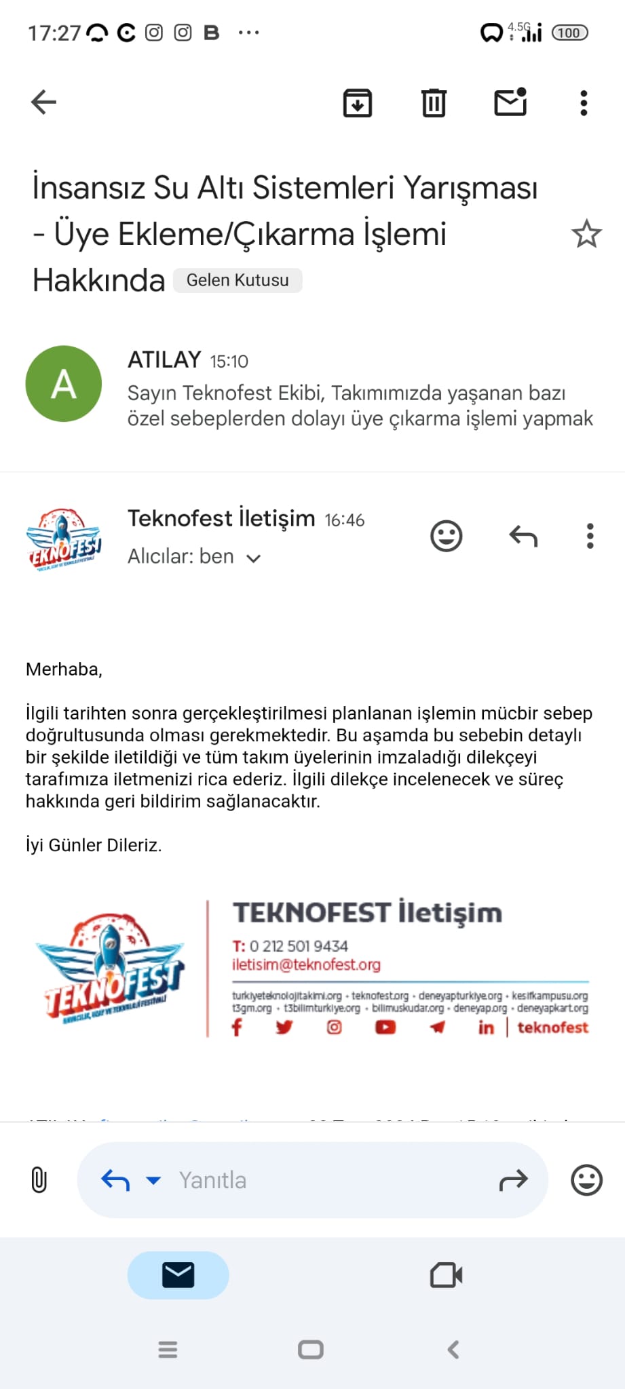
ProjeResimleri/IMG-20240722-WA0004.jpg
