OmerFaruk-Celik/ATILAY/ProjeResimleri/IMG-20240722-WA0006.jpg

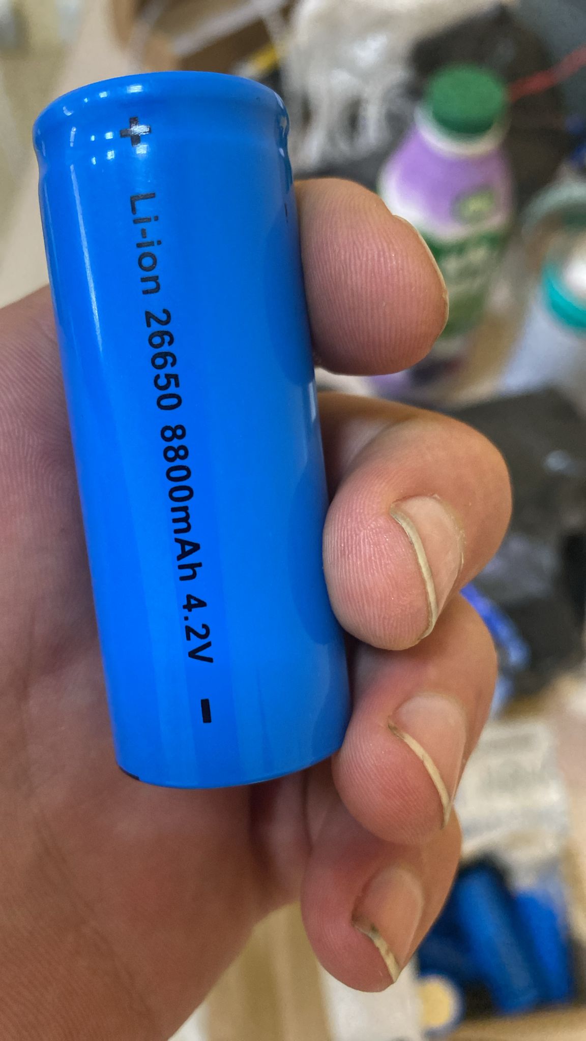
ProjeResimleri/IMG-20240722-WA0006.jpg
