OmerFaruk-Celik/ATILAY/ProjeResimleri/IMG-20240722-WA0007.jpg

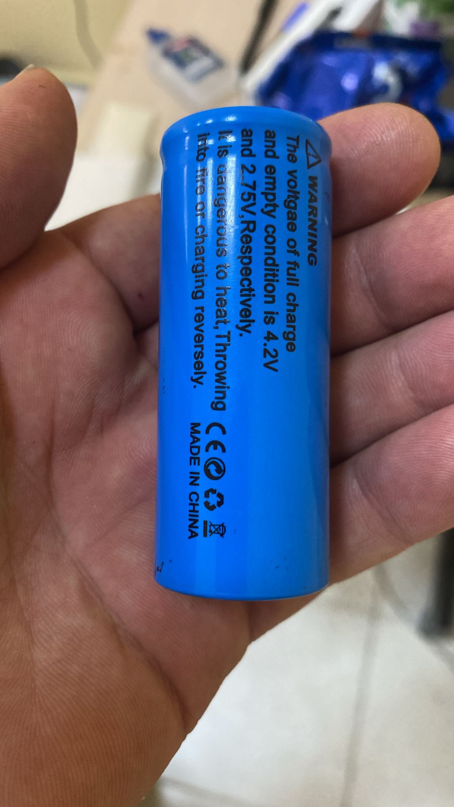
ProjeResimleri/IMG-20240722-WA0007.jpg
