OmerFaruk-Celik/ATILAY/ProjeResimleri/IMG-20240722-WA0008.jpg

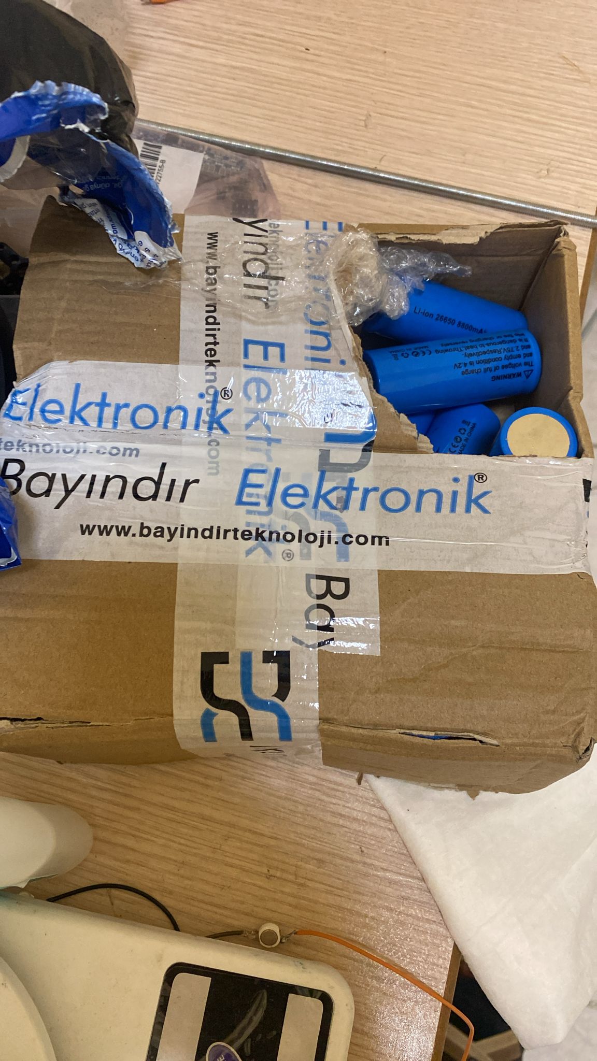
ProjeResimleri/IMG-20240722-WA0008.jpg
