OmerFaruk-Celik/ATILAY/ProjeResimleri/IMG-20240722-WA0010.jpg

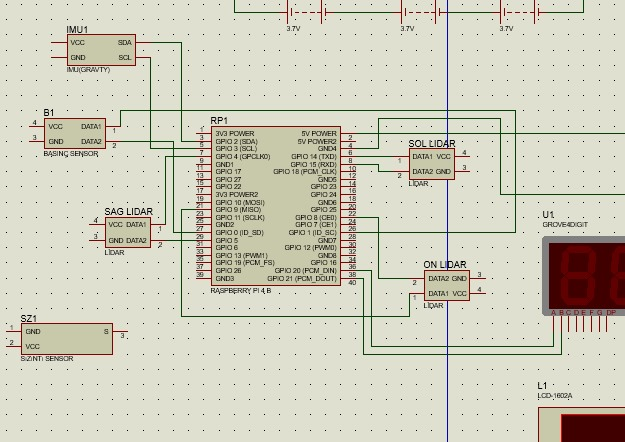
ProjeResimleri/IMG-20240722-WA0010.jpg
