OmerFaruk-Celik/ATILAY/ProjeResimleri/IMG-20240723-WA0000.jpg

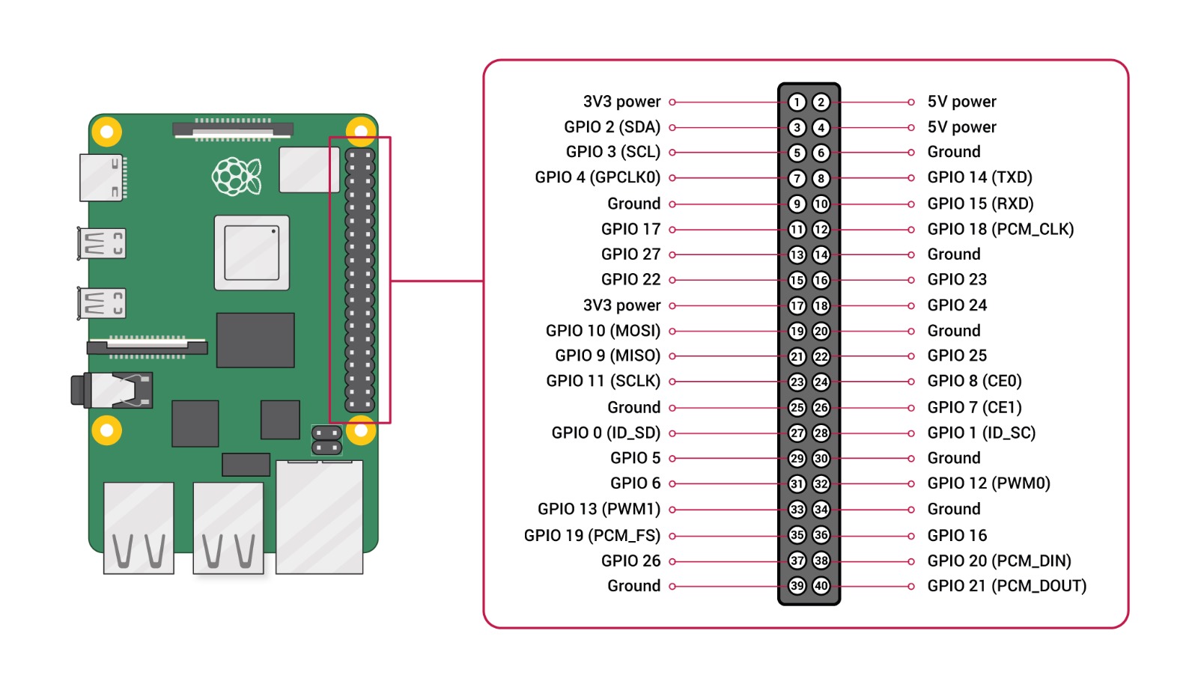
ProjeResimleri/IMG-20240723-WA0000.jpg
