OmerFaruk-Celik/ATILAY/ProjeResimleri/IMG-20240725-WA0012.jpg

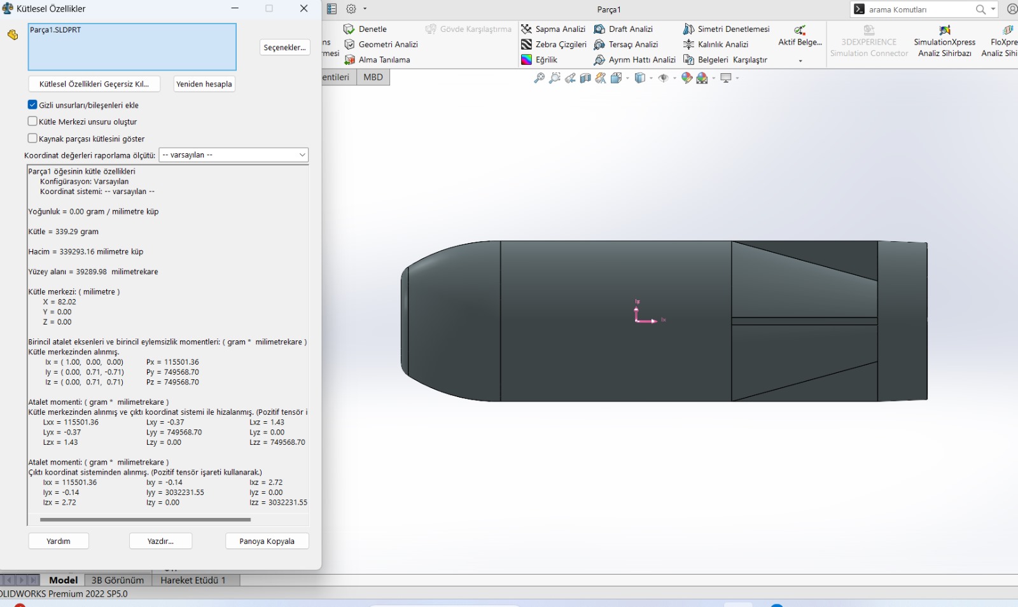
ProjeResimleri/IMG-20240725-WA0012.jpg
