OmerFaruk-Celik/ATILAY/ProjeResimleri/IMG-20240725-WA0013.jpg

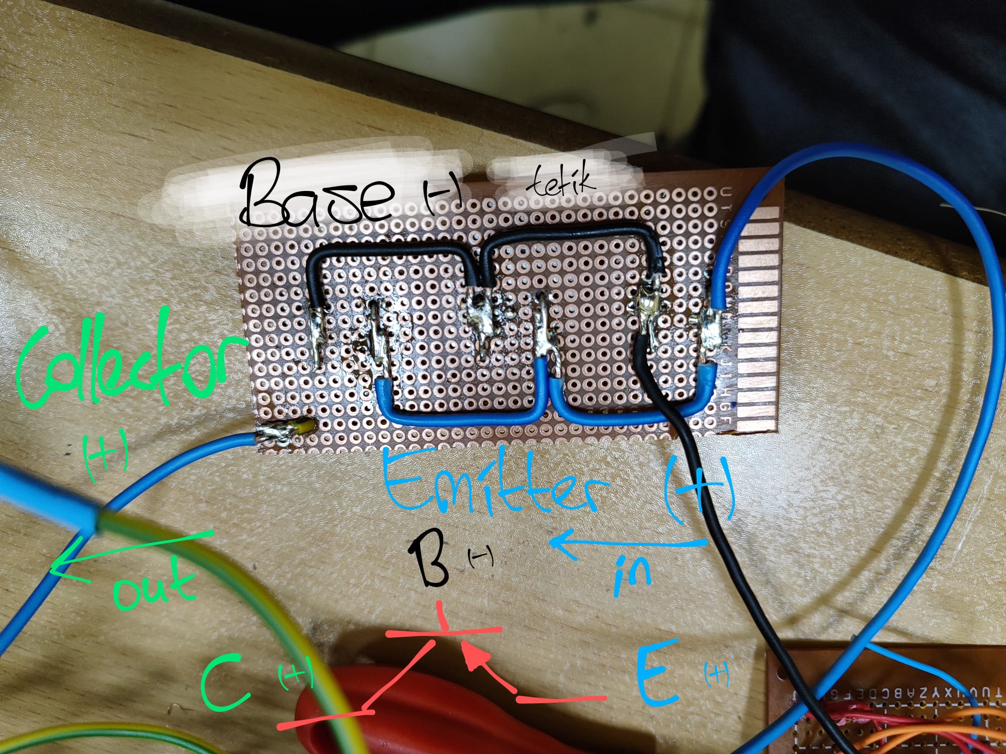
ProjeResimleri/IMG-20240725-WA0013.jpg
