OmerFaruk-Celik/ATILAY/ProjeResimleri/IMG-20240725-WA0014.jpg

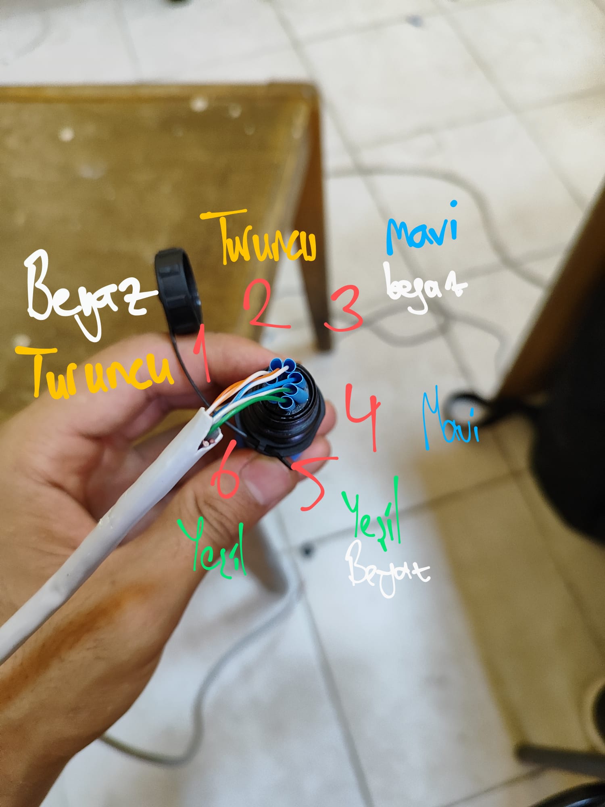
ProjeResimleri/IMG-20240725-WA0014.jpg
