OmerFaruk-Celik/ATILAY/ProjeResimleri/IMG-20240725-WA0015.jpg

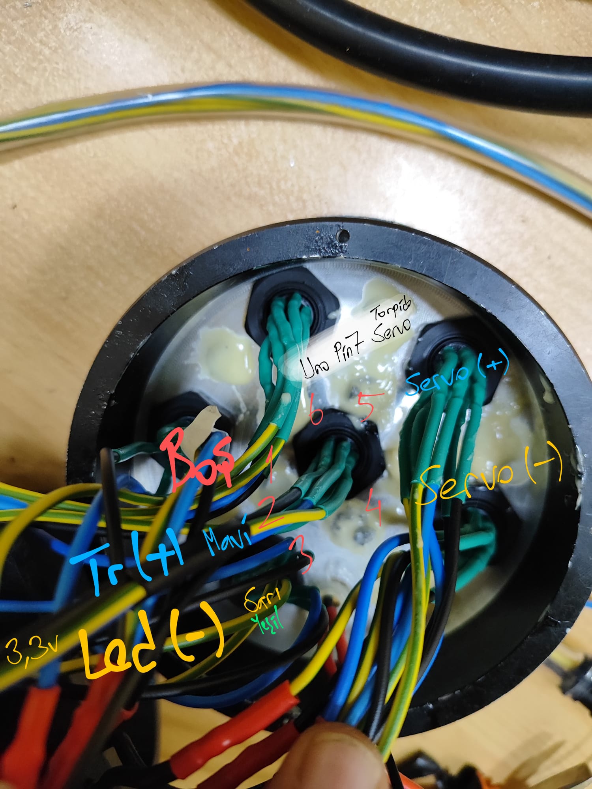
ProjeResimleri/IMG-20240725-WA0015.jpg
