OmerFaruk-Celik/ATILAY/ProjeResimleri/IMG-20240725-WA0016.jpg

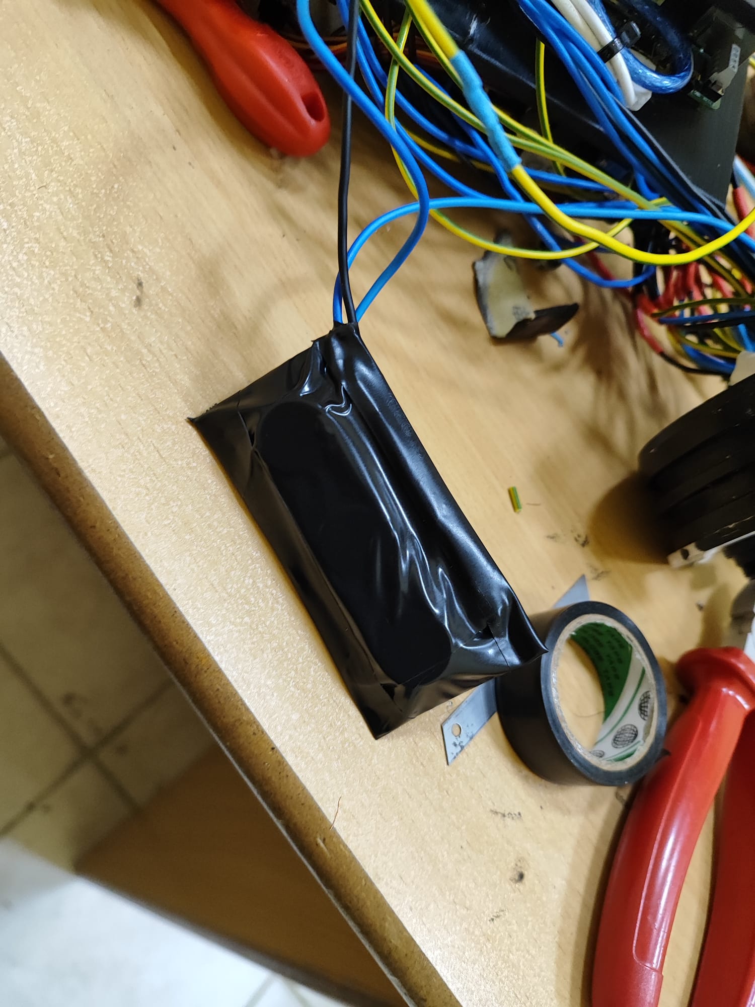
ProjeResimleri/IMG-20240725-WA0016.jpg
