OmerFaruk-Celik/ATILAY/ProjeResimleri/IMG-20240725-WA0017.jpg

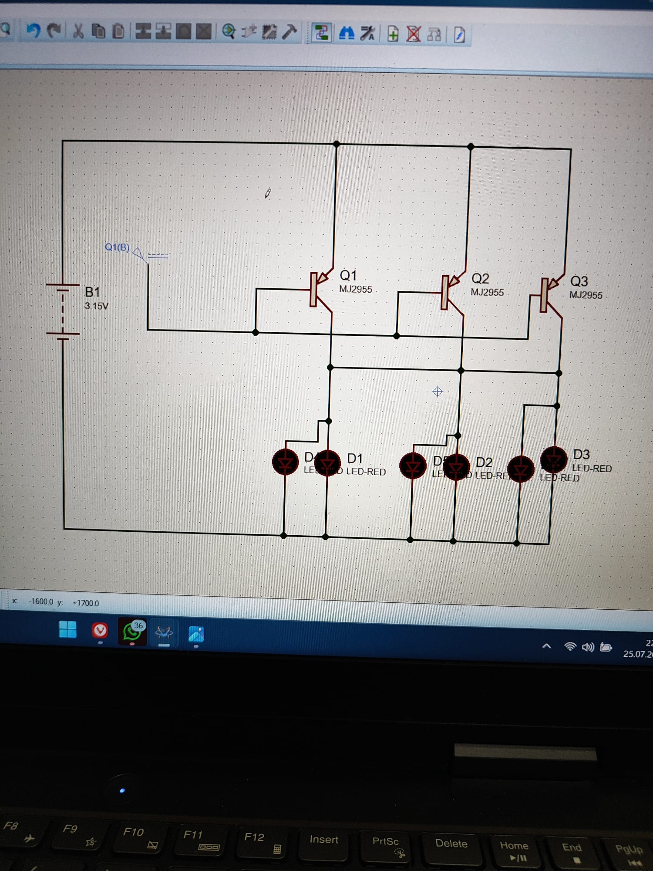
ProjeResimleri/IMG-20240725-WA0017.jpg
