OmerFaruk-Celik/ATILAY/ProjeResimleri/IMG-20240725-WA0018.jpg

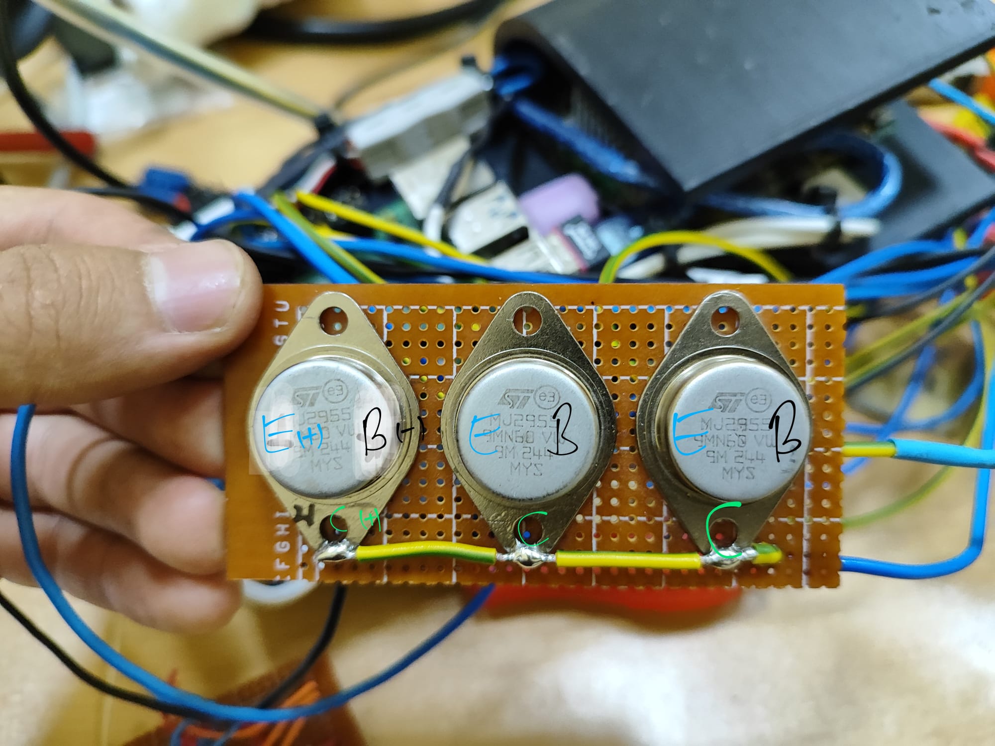
ProjeResimleri/IMG-20240725-WA0018.jpg
