OmerFaruk-Celik/ATILAY/ProjeResimleri/IMG-20240726-WA0001.jpg

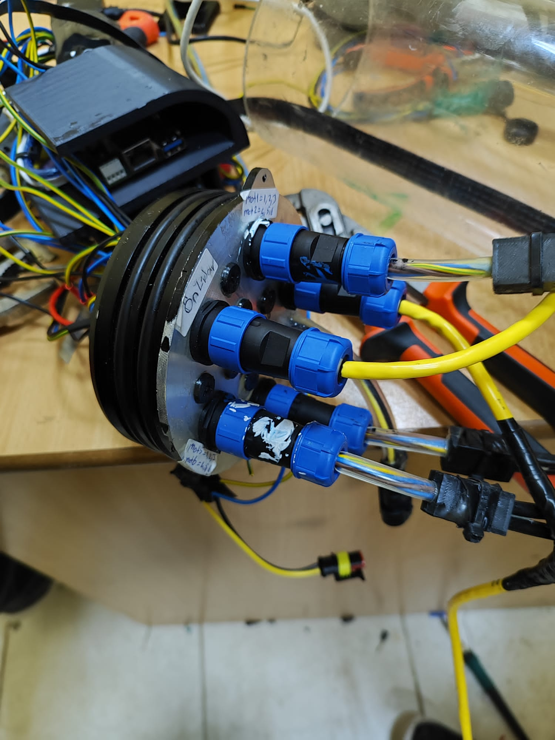
ProjeResimleri/IMG-20240726-WA0001.jpg
