OmerFaruk-Celik/ATILAY/ProjeResimleri/IMG-20240806-WA0000.jpg

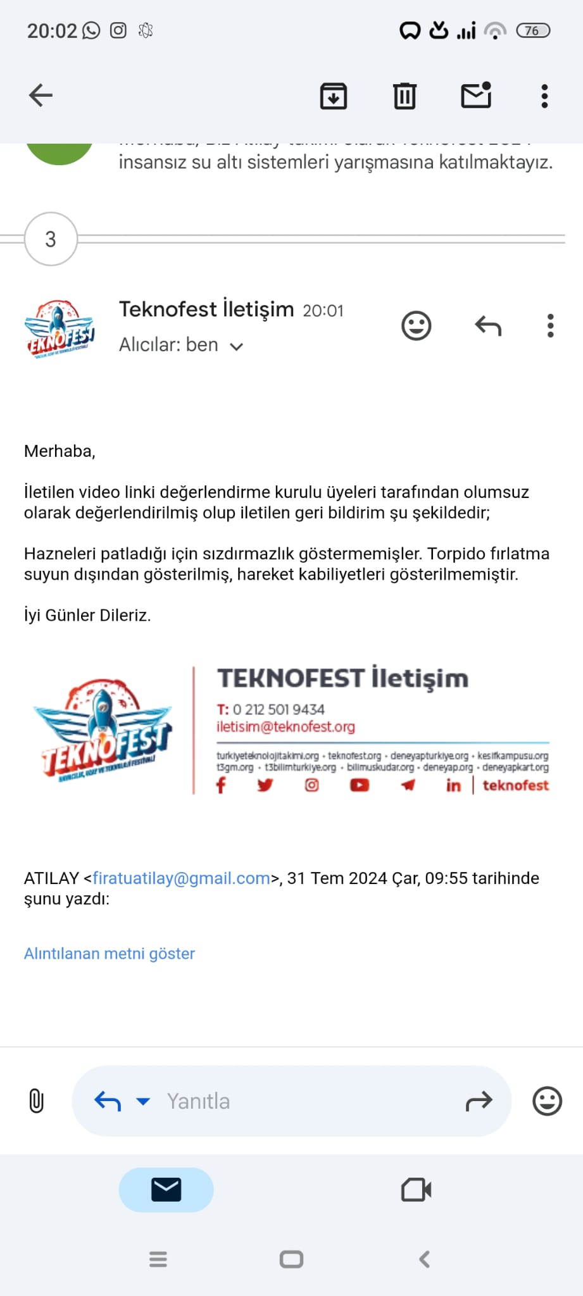
ProjeResimleri/IMG-20240806-WA0000.jpg
