OmerFaruk-Celik/ATILAY/ProjeResimleri/WhatsApp Image 2024-06-30 at 16.40.59.jpeg

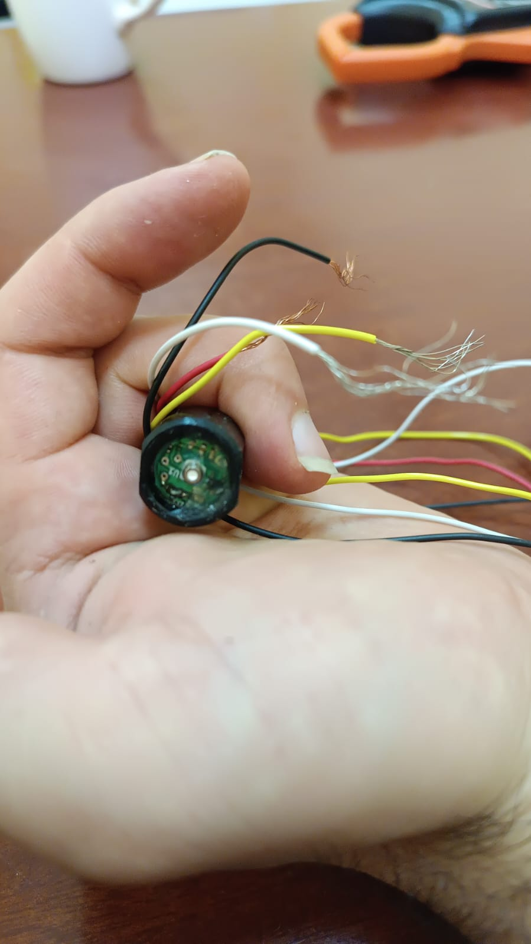
ProjeResimleri/WhatsApp Image 2024-06-30 at 16.40.59.jpeg
