OmerFaruk-Celik/ATILAY/ProjeResimleri/WhatsApp Image 2024-06-30 at 16.41.17.jpeg

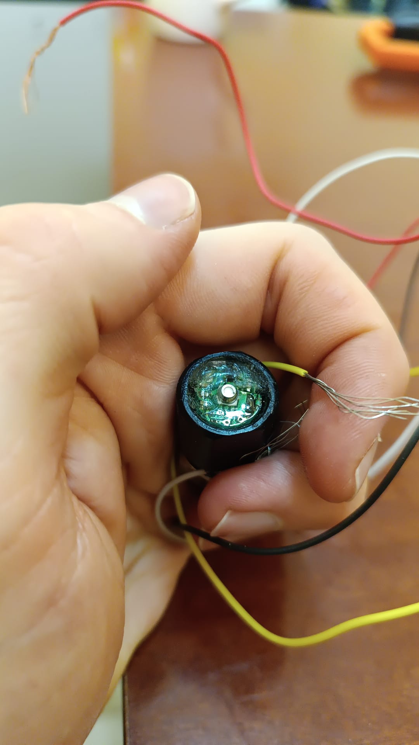
ProjeResimleri/WhatsApp Image 2024-06-30 at 16.41.17.jpeg
