OmerFaruk-Celik/ATILAY/ProjeResimleri/WhatsApp Image 2024-07-09 at 11.06.11.jpeg

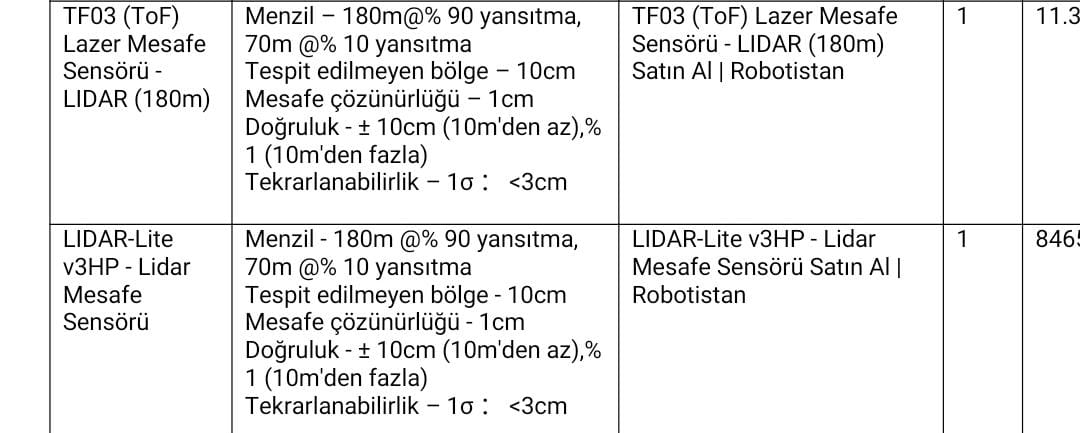
ProjeResimleri/WhatsApp Image 2024-07-09 at 11.06.11.jpeg
