OmerFaruk-Celik/ATILAY/ProjeResimleri/WhatsApp Image 2024-07-23 at 00.09.40(1).jpeg

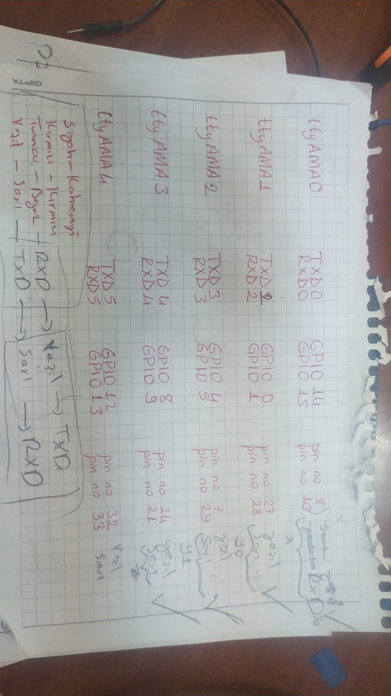
ProjeResimleri/WhatsApp Image 2024-07-23 at 00.09.40(1).jpeg
