OmerFaruk-Celik/ATILAY/ProjeVideolari/STK-20240610-WA0001.webp

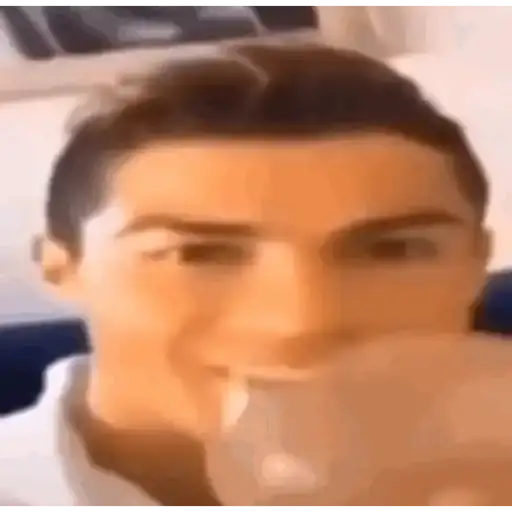
ProjeVideolari/STK-20240610-WA0001.webp
