OmerFaruk-Celik/ATILAY/ProjeVideolari/STK-20240613-WA0011.webp

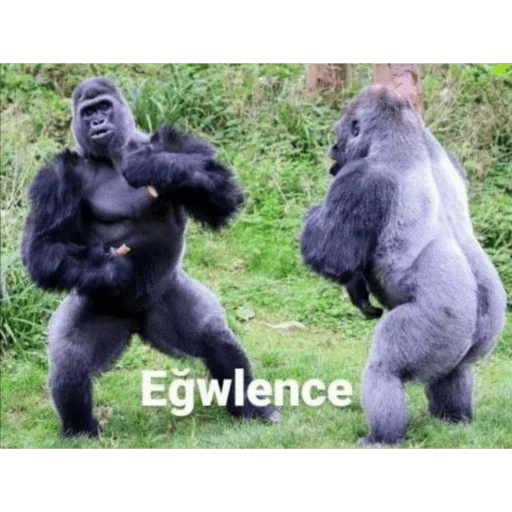
ProjeVideolari/STK-20240613-WA0011.webp
