OmerFaruk-Celik/ATILAY/ProjeVideolari/STK-20240613-WA0012.webp

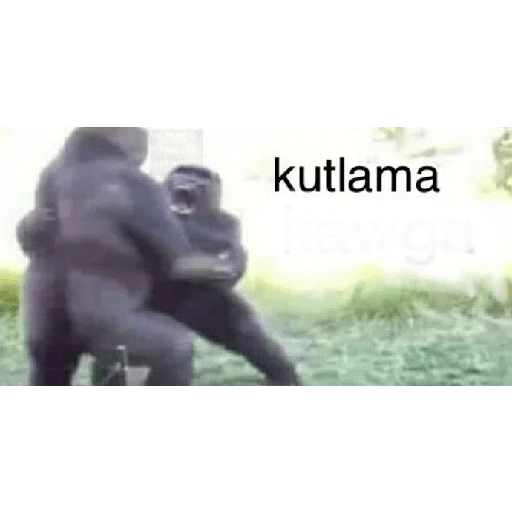
ProjeVideolari/STK-20240613-WA0012.webp
