OmerFaruk-Celik/ATILAY/ProjeVideolari/STK-20240613-WA0013.webp

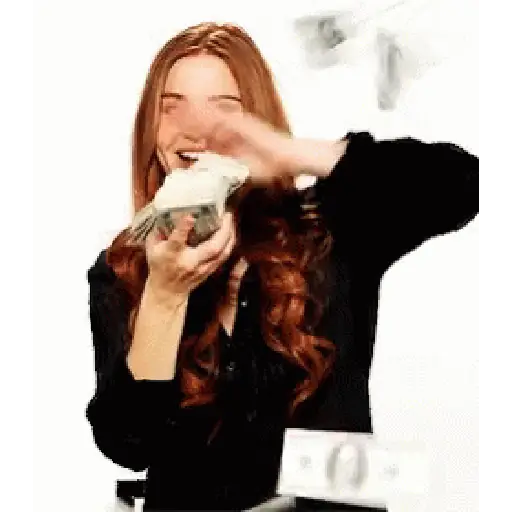
ProjeVideolari/STK-20240613-WA0013.webp
