OmerFaruk-Celik/ATILAY/ProjeVideolari/STK-20240613-WA0014.webp

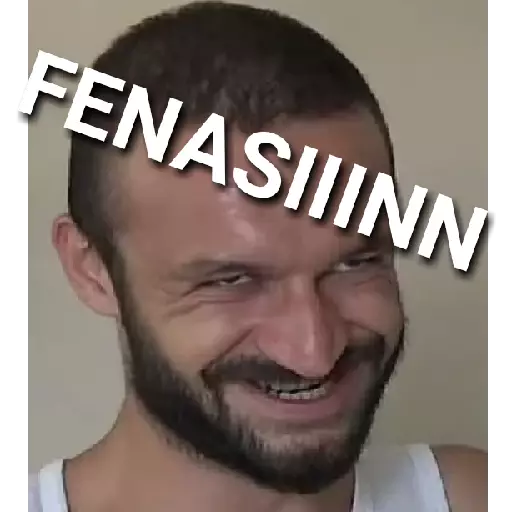
ProjeVideolari/STK-20240613-WA0014.webp
