OmerFaruk-Celik/ATILAY/ProjeVideolari/STK-20240613-WA0015.webp

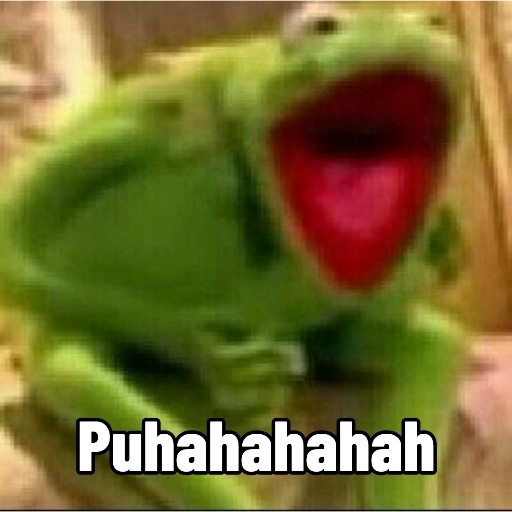
ProjeVideolari/STK-20240613-WA0015.webp
