OmerFaruk-Celik/ATILAY/ProjeVideolari/STK-20240613-WA0016.webp

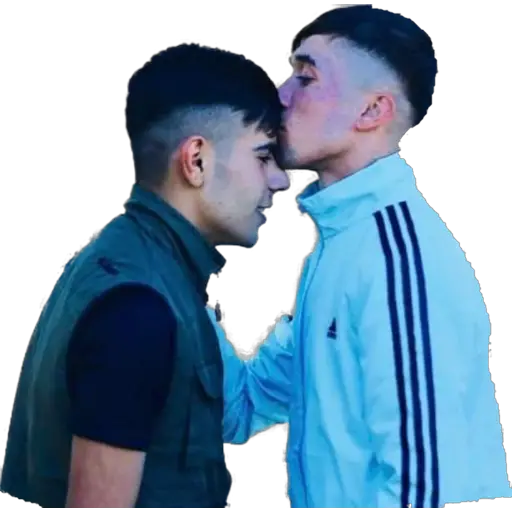
ProjeVideolari/STK-20240613-WA0016.webp
