OmerFaruk-Celik/ATILAY/ProjeVideolari/STK-20240613-WA0017.webp

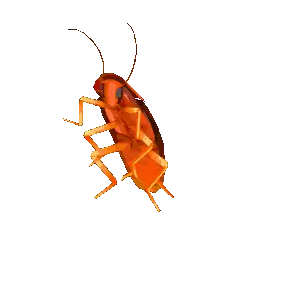
ProjeVideolari/STK-20240613-WA0017.webp
