OmerFaruk-Celik/ATILAY/ProjeVideolari/STK-20240613-WA0018.webp

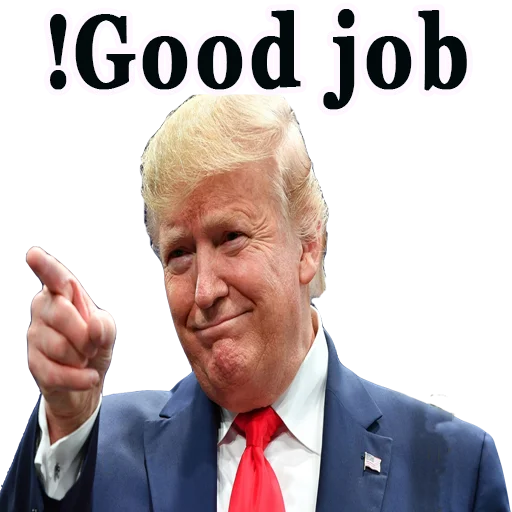
ProjeVideolari/STK-20240613-WA0018.webp
