OmerFaruk-Celik/ATILAY/ProjeVideolari/STK-20240613-WA0020.webp

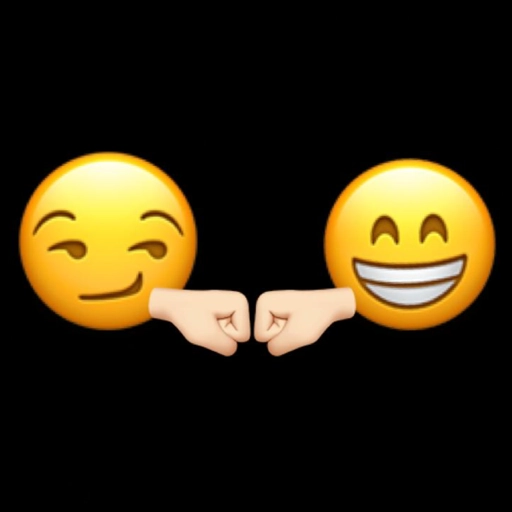
ProjeVideolari/STK-20240613-WA0020.webp
