OmerFaruk-Celik/ATILAY/ProjeVideolari/STK-20240613-WA0021.webp

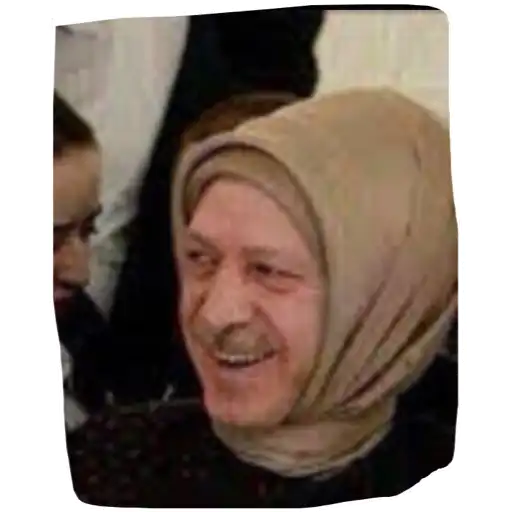
ProjeVideolari/STK-20240613-WA0021.webp
