OmerFaruk-Celik/ATILAY/ProjeVideolari/STK-20240613-WA0022.webp

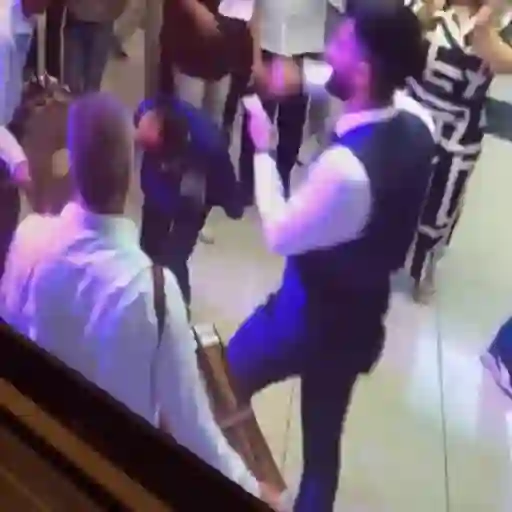
ProjeVideolari/STK-20240613-WA0022.webp
