OmerFaruk-Celik/ATILAY/ProjeVideolari/STK-20240613-WA0023.webp

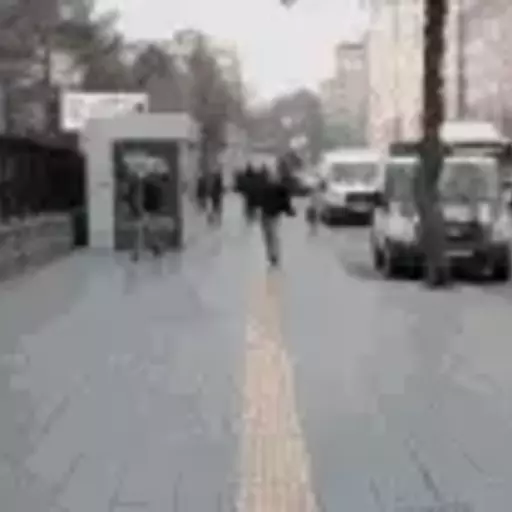
ProjeVideolari/STK-20240613-WA0023.webp
