OmerFaruk-Celik/ATILAY/ProjeVideolari/STK-20240613-WA0025.webp

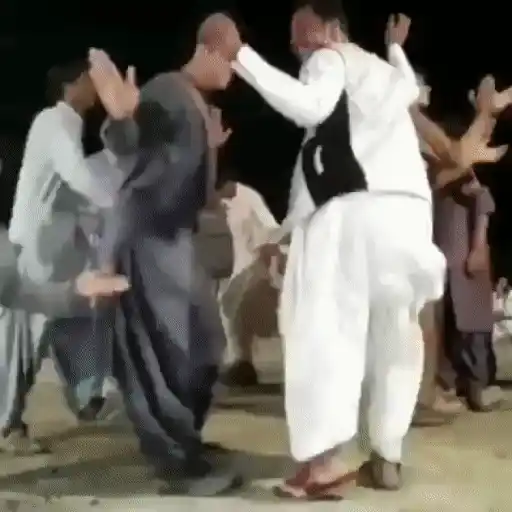
ProjeVideolari/STK-20240613-WA0025.webp
