OmerFaruk-Celik/ATILAY/ProjeVideolari/STK-20240613-WA0026.webp

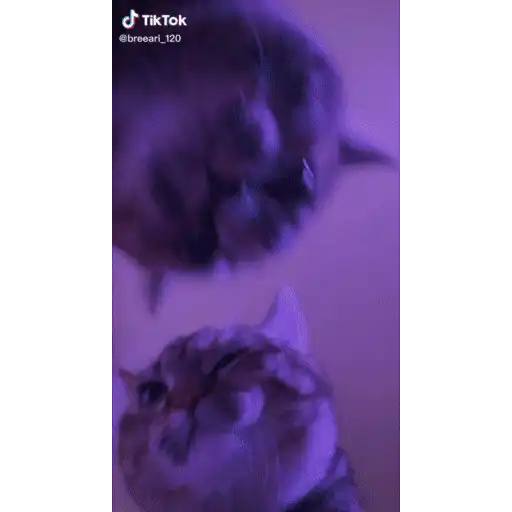
ProjeVideolari/STK-20240613-WA0026.webp
