OmerFaruk-Celik/ATILAY/ProjeVideolari/STK-20240613-WA0027.webp

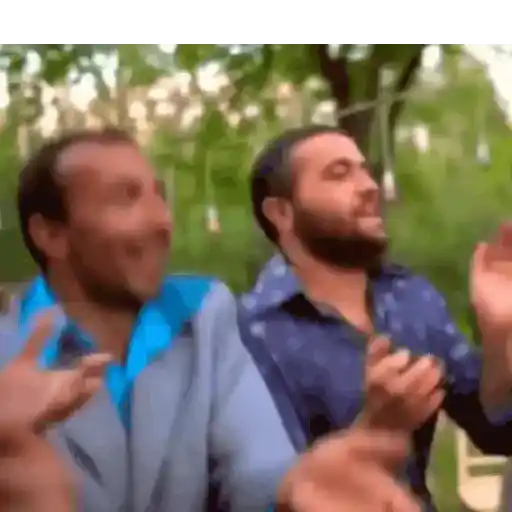
ProjeVideolari/STK-20240613-WA0027.webp
